marcuswu/Curta-Type-I-3x/Mods/Printed Lettering/selector shaft top/mmu selector shaft top.3mf

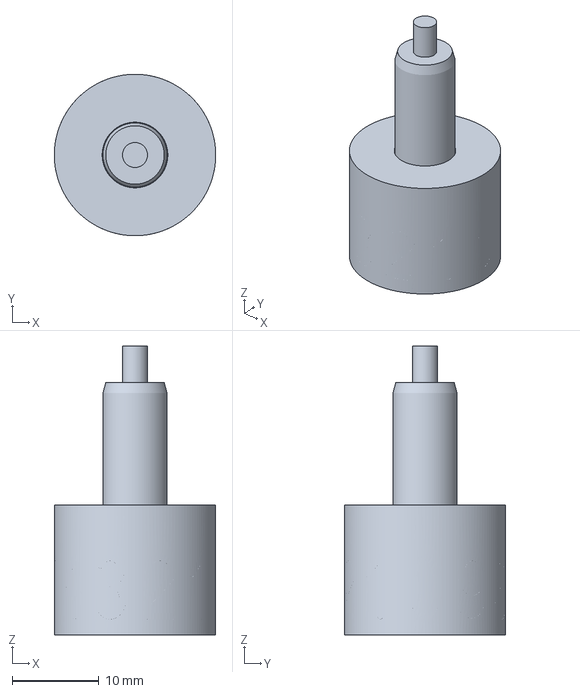
[picture p18: CAD file, 2025-07-06]
Mods/Printed Lettering/selector shaft top/mmu selector shaft top.3mf
18.6 x 18.6 x 33.3 mm
