marcuswu/Curta-Type-I-3x/Mods/Printed Lettering/upper housing/upper housing - digit 7.stl

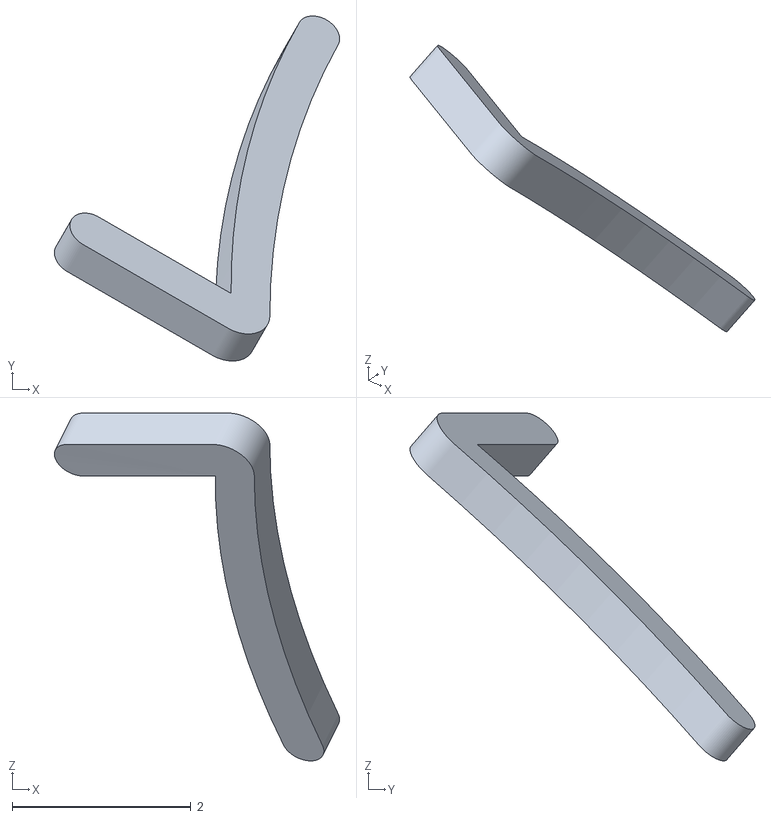
[picture p19: CAD file, 2025-07-06]
Mods/Printed Lettering/upper housing/upper housing - digit 7.stl
3.19 x 3.86 x 3.89
