marcuswu/Curta-Type-I-3x/Mods/Printed Lettering/upper outer sleeve/upper outer sleeve - A.stl

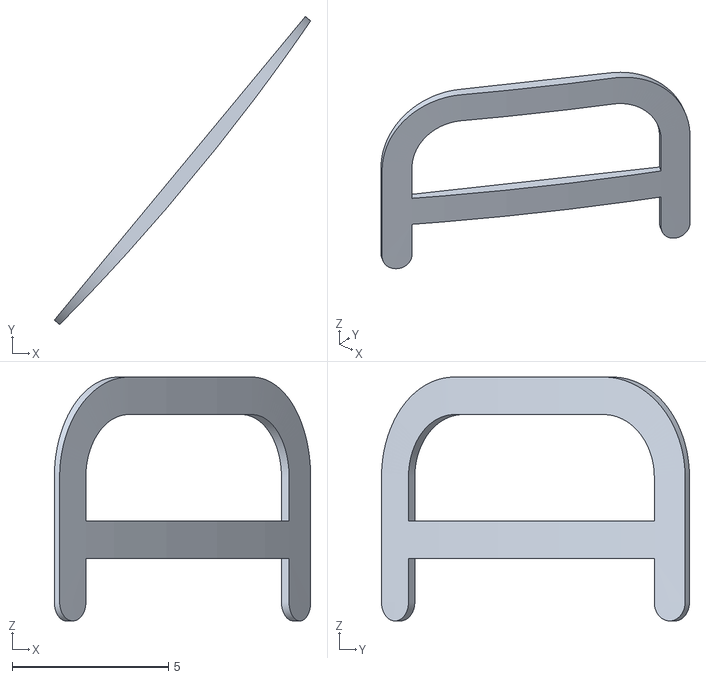
[picture p20: CAD file, 2025-07-06]
Mods/Printed Lettering/upper outer sleeve/upper outer sleeve - A.stl
8.20 x 9.85 x 7.80
