marcuswu/Curta-Type-I-3x/STLs/10 - Upper Frame/frame support x3.stl

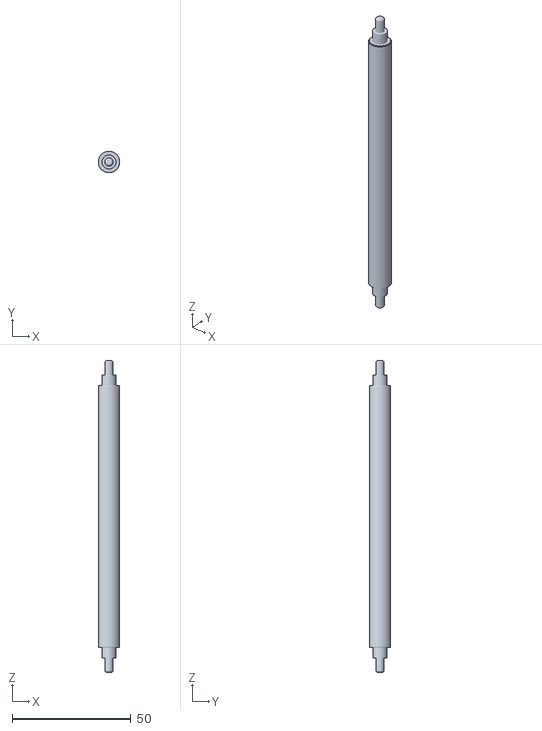
[picture p21: CAD file, 2022-03-31]
STLs/10 - Upper Frame/frame support x3.stl
9.00 x 9.00 x 131.2
