marcuswu/Curta-Type-I-3x/STLs/11 - Assemble Step Drum/step drum joining pin x3.stl

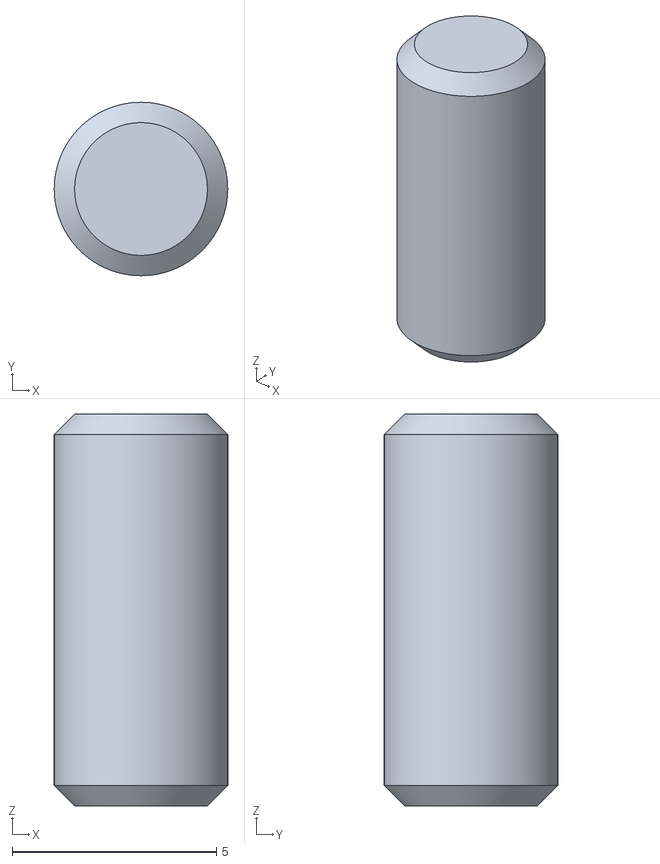
[picture p22: CAD file, 2022-03-31]
STLs/11 - Assemble Step Drum/step drum joining pin x3.stl
4.25 x 4.25 x 9.60
