marcuswu/Curta-Type-I-3x/STLs/12 - Step Drum & Bearing Plate/bearing plate.stl

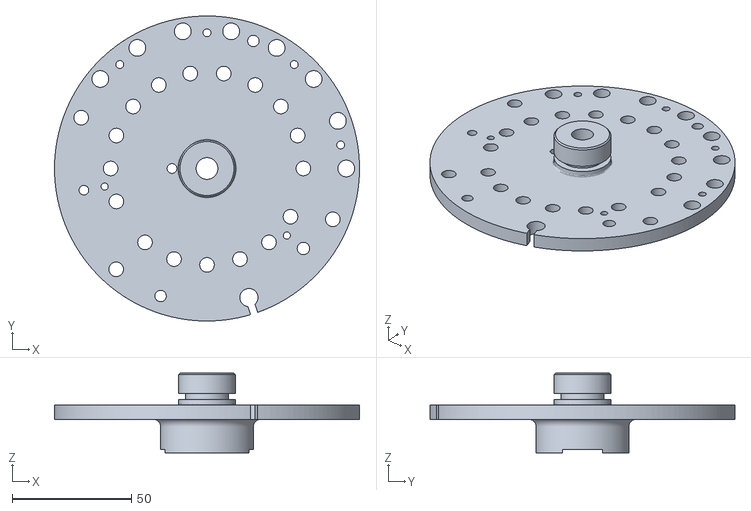
[picture p23: CAD file, 2022-03-31]
STLs/12 - Step Drum & Bearing Plate/bearing plate.stl
128.1 x 128.1 x 33.6
