marcuswu/Curta-Type-I-3x/STLs/15 - Zero Positioning Disc/zero positioning disc securing spring.stl

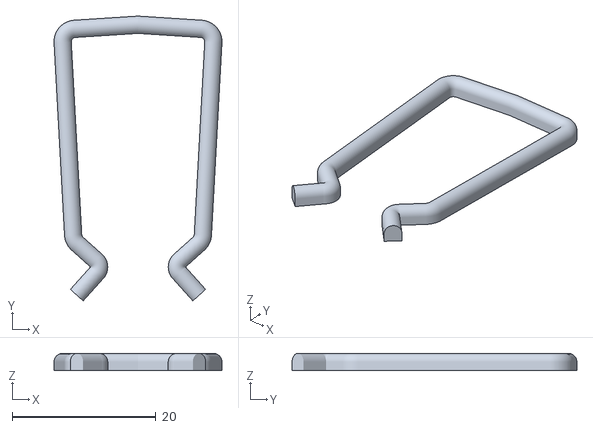
[picture p24: CAD file, 2022-03-31]
STLs/15 - Zero Positioning Disc/zero positioning disc securing spring.stl
23.3 x 39.6 x 2.40
