marcuswu/Curta-Type-I-3x/STLs/18 - Zero Positioning Disc Pin/zero positioning disc pin.stl

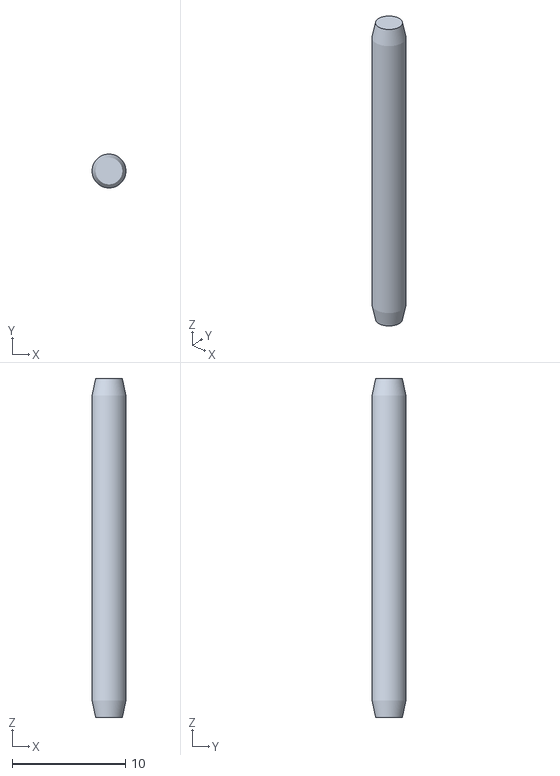
[picture p25: CAD file, 2022-03-31]
STLs/18 - Zero Positioning Disc Pin/zero positioning disc pin.stl
3.00 x 3.00 x 30.0
