marcuswu/Curta-Type-I-3x/STLs/21 - Transmission Shafts/transmission shaft 10208.stl

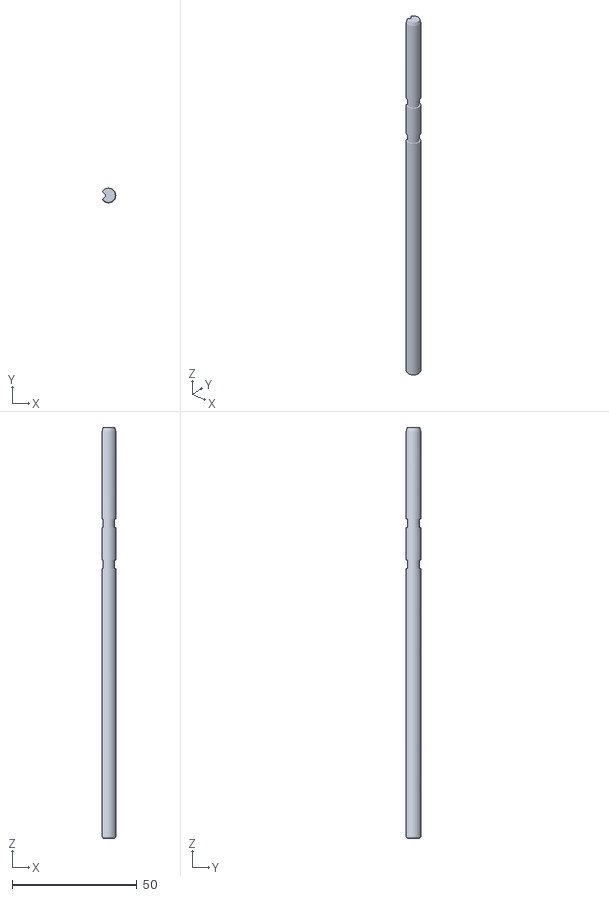
[picture p26: CAD file, 2022-03-31]
STLs/21 - Transmission Shafts/transmission shaft 10208.stl
5.45 x 5.89 x 165.0
