marcuswu/Curta-Type-I-3x/STLs/26 - Cover Ring/cover ring.stl

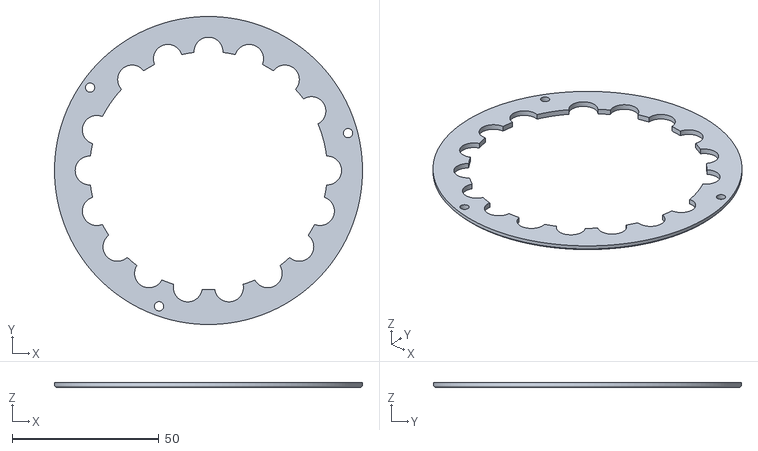
[picture p27: CAD file, 2022-03-31]
STLs/26 - Cover Ring/cover ring.stl
104.9 x 104.9 x 1.80
