marcuswu/Curta-Type-I-3x/STLs/27 - Assemble Reversing Lever/reversing lever knob.stl

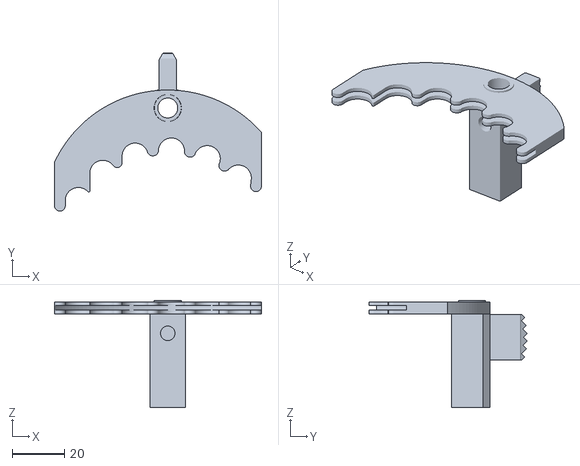
[picture p28: CAD file, 2022-03-31]
STLs/27 - Assemble Reversing Lever/reversing lever knob.stl
79.5 x 60.8 x 41.1
