marcuswu/Curta-Type-I-3x/STLs/29 - Assemble Carry Levers/tens slide bearing x15.stl

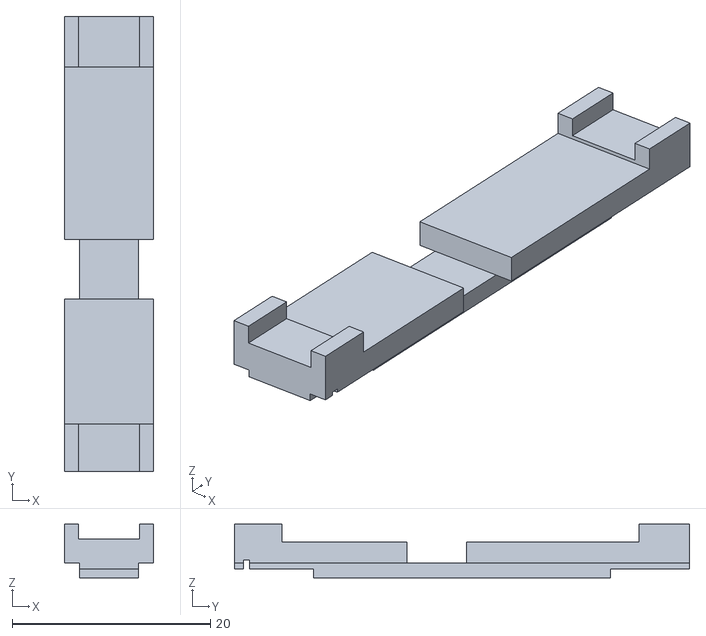
[picture p29: CAD file, 2022-03-31]
STLs/29 - Assemble Carry Levers/tens slide bearing x15.stl
9.00 x 45.9 x 5.40
