marcuswu/Curta-Type-I-3x/STLs/31 - Assemble Input Selectors/selector knob x8.stl

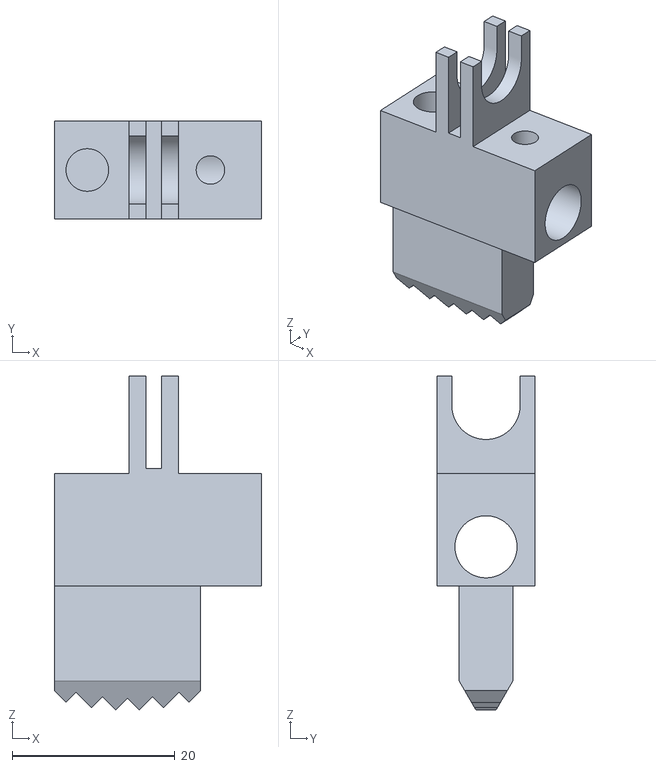
[picture p30: CAD file, 2022-03-31]
STLs/31 - Assemble Input Selectors/selector knob x8.stl
25.5 x 12.0 x 41.1
