marcuswu/Curta-Type-I-3x/STLs/32 - Input Selectors/selector shaft bearing x8.stl

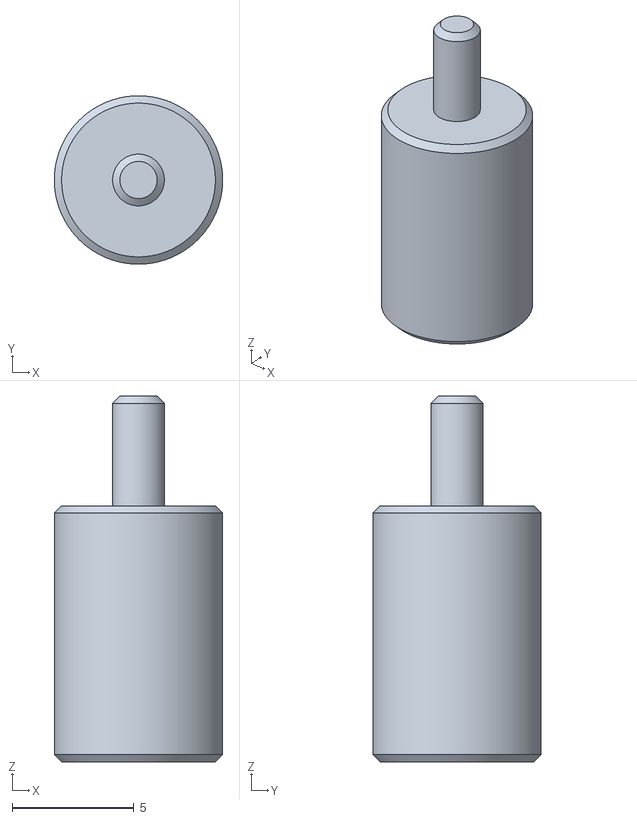
[picture p31: CAD file, 2022-03-31]
STLs/32 - Input Selectors/selector shaft bearing x8.stl
6.90 x 6.90 x 15.0
