marcuswu/Curta-Type-I-3x/STLs/33 - Upper Sleeve/upper outer sleeve.stl

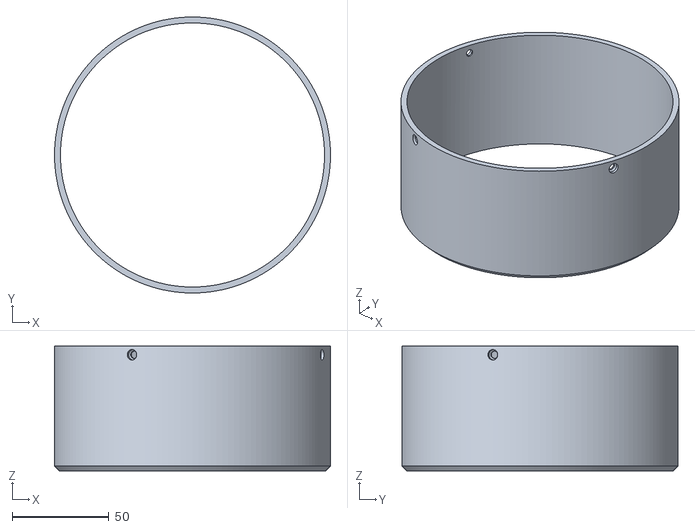
[picture p32: CAD file, 2022-03-31]
STLs/33 - Upper Sleeve/upper outer sleeve.stl
142.5 x 142.5 x 64.5
