marcuswu/Curta-Type-I-3x/STLs/34 - Lower Housing & Base Plate/lower housing.stl

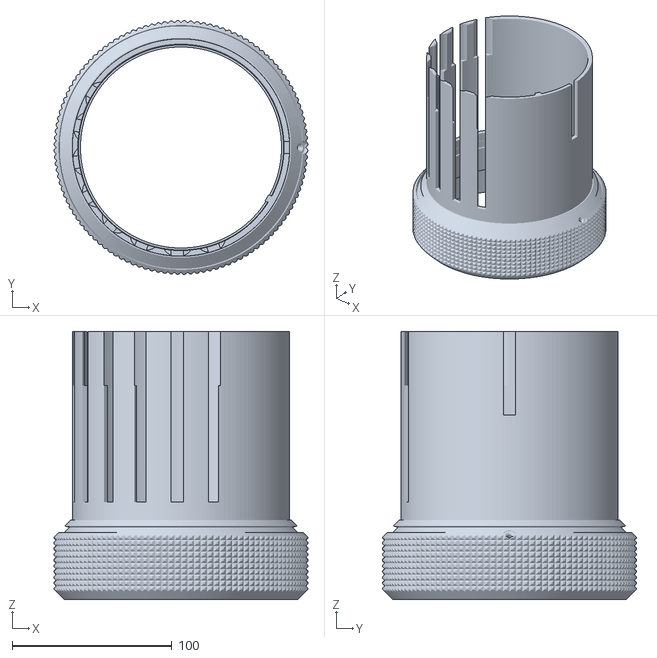
[picture p33: CAD file, 2022-03-31]
STLs/34 - Lower Housing & Base Plate/lower housing.stl
159.0 x 159.0 x 168.0
