marcuswu/Curta-Type-I-3x/STLs/37 - Clearing Cover/clearing cover.stl

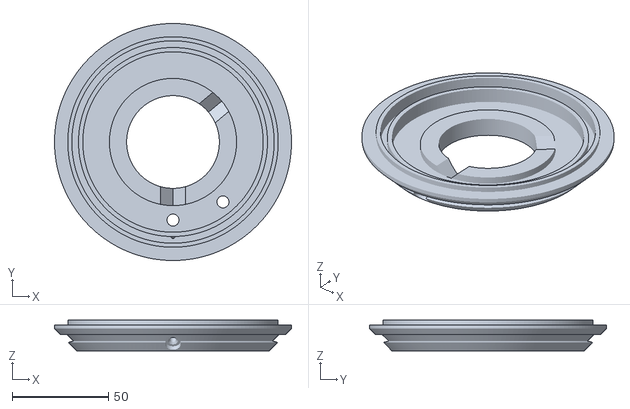
[picture p34: CAD file, 2022-03-31]
STLs/37 - Clearing Cover/clearing cover.stl
123.0 x 123.0 x 15.9
