marcuswu/Curta-Type-I-3x/STLs/38 - Carriage Body/carriage body.stl

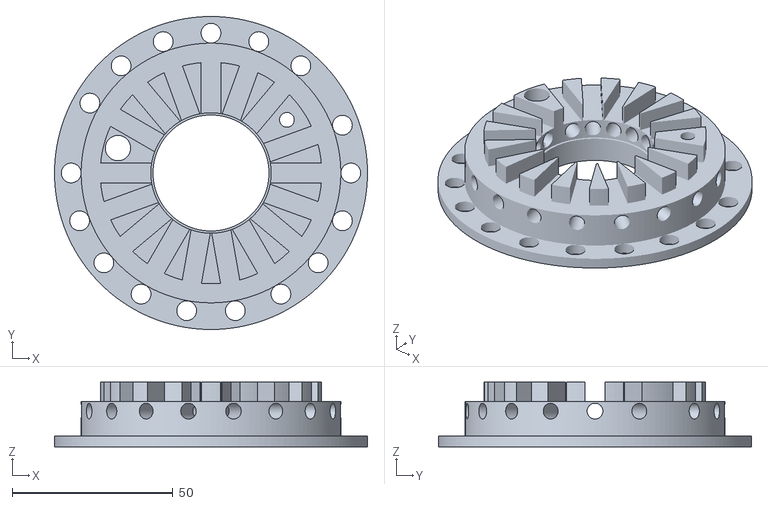
[picture p35: CAD file, 2022-03-31]
STLs/38 - Carriage Body/carriage body.stl
97.5 x 97.5 x 20.1
