marcuswu/Curta-Type-I-3x/STLs/39 - Clearing Stop Pin & Digit Axles/digits axle x17.stl

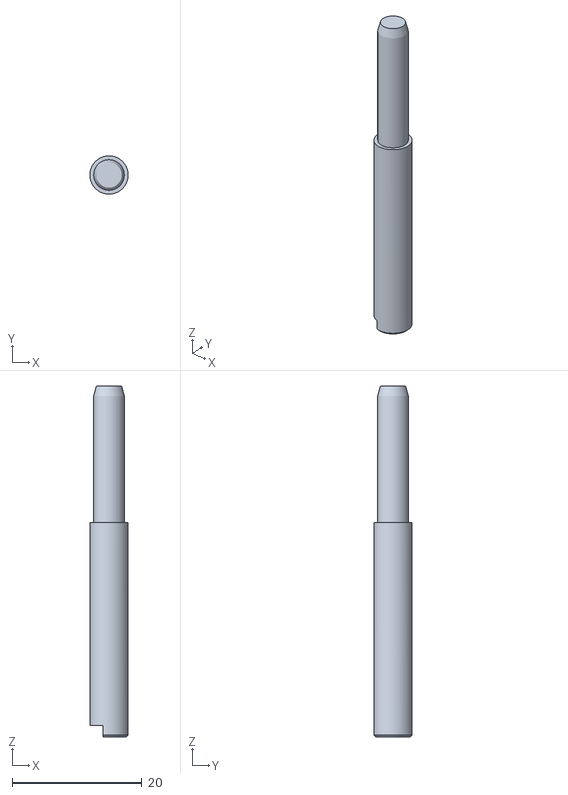
[picture p36: CAD file, 2022-03-31]
STLs/39 - Clearing Stop Pin & Digit Axles/digits axle x17.stl
5.89 x 5.89 x 54.0
