marcuswu/Curta-Type-I-3x/STLs/41 - Spider Spring/spider spring.stl

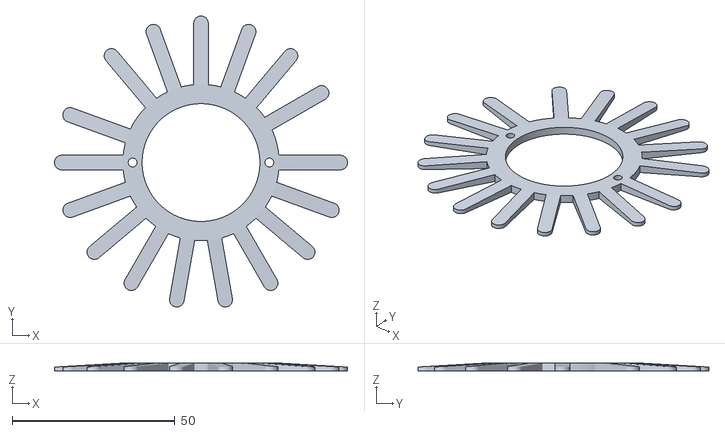
[picture p37: CAD file, 2022-03-31]
STLs/41 - Spider Spring/spider spring.stl
90.0 x 89.4 x 2.42
