marcuswu/Curta-Type-I-3x/STLs/42 - Digit Cover & Upper Housing/upper housing.stl

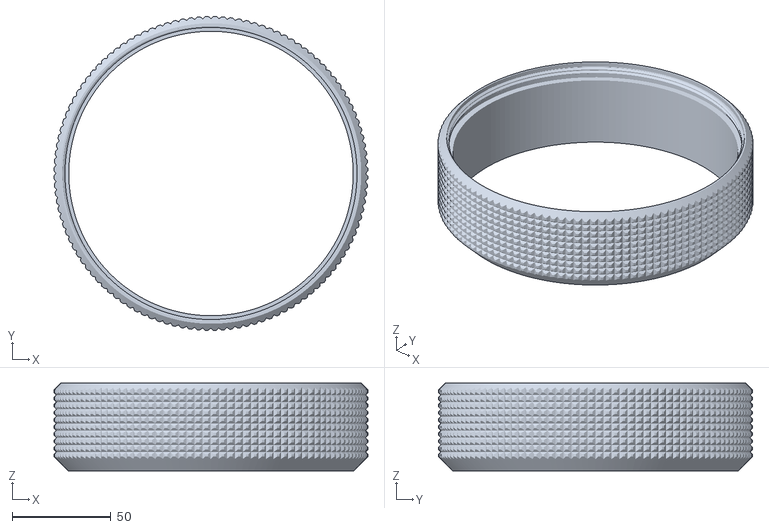
[picture p38: CAD file, 2022-03-31]
STLs/42 - Digit Cover & Upper Housing/upper housing.stl
159.0 x 159.0 x 44.4
