marcuswu/Curta-Type-I-3x/STLs/47 - Carriage Spring/spring sleeve c-clip.stl

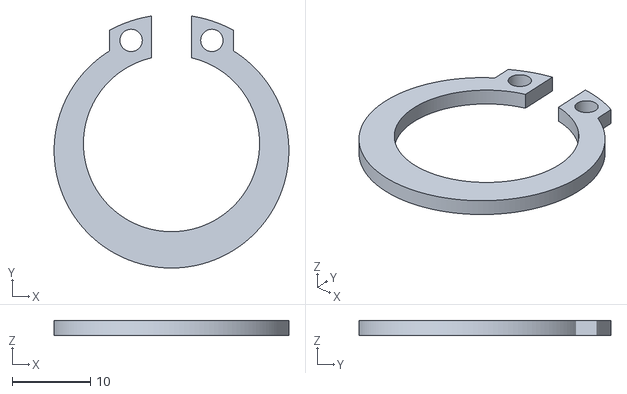
[picture p39: CAD file, 2022-03-31]
STLs/47 - Carriage Spring/spring sleeve c-clip.stl
30.0 x 32.2 x 1.95
