marcuswu/Curta-Type-I-3x/STLs/49 - Crank Handle/crank handle pin.stl

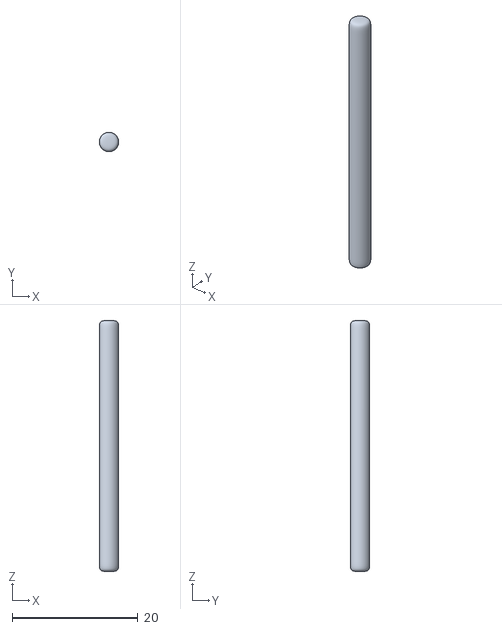
[picture p40: CAD file, 2022-03-31]
STLs/49 - Crank Handle/crank handle pin.stl
3.10 x 3.10 x 40.0
