marcuswu/Curta-Type-I-3x/STLs/50 - Decimal Markers/position marker x10.stl

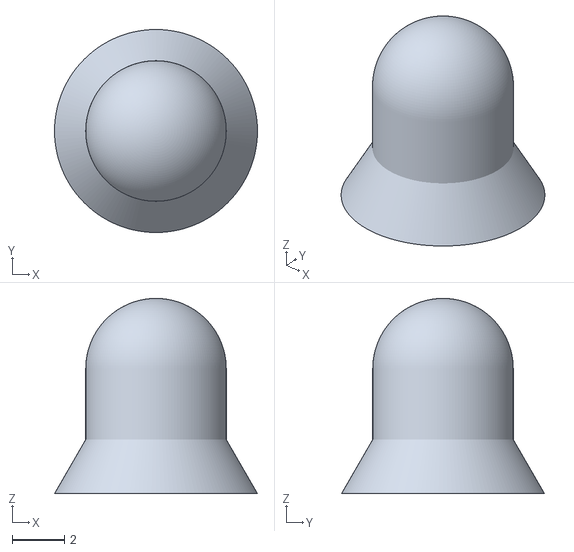
[picture p41: CAD file, 2022-03-31]
STLs/50 - Decimal Markers/position marker x10.stl
7.80 x 7.80 x 7.50
