marcuswu/Curta-Type-I-3x/STLs/8 - Assemble Tens Bell/tens bell.stl

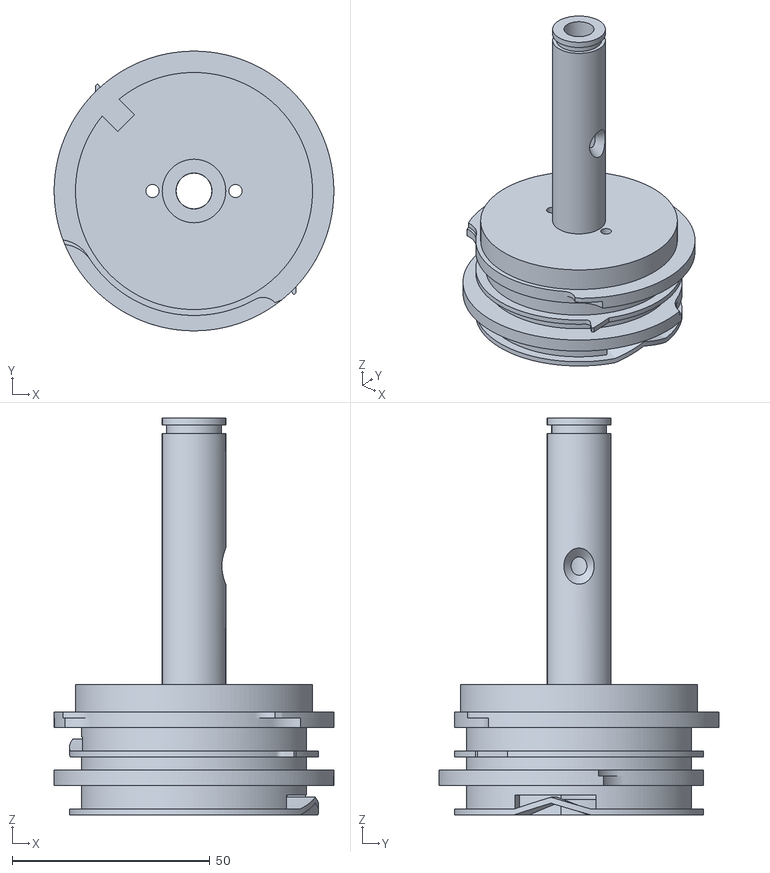
[picture p42: CAD file, 2022-03-31]
STLs/8 - Assemble Tens Bell/tens bell.stl
70.8 x 70.8 x 100.5
