marcuswu/Curta-Type-I-3x/STLs/9 - Tens Bell & Main Body/tens bell c-clip.stl

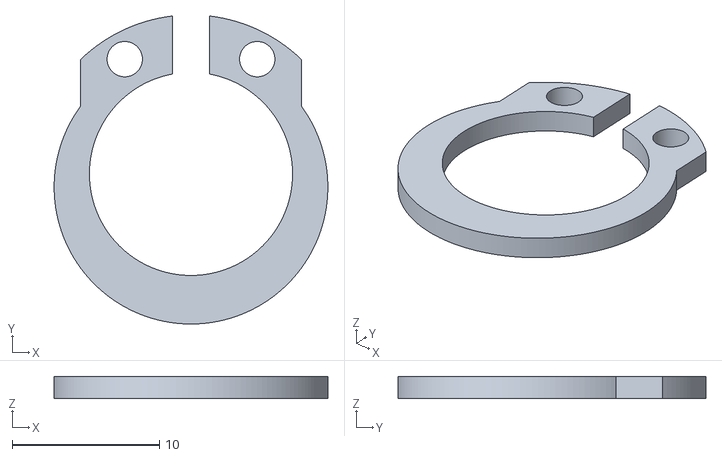
[picture p43: CAD file, 2022-03-31]
STLs/9 - Tens Bell & Main Body/tens bell c-clip.stl
18.6 x 20.9 x 1.50
