marcuswu/Curta-Type-I-3x/Manual/Painting/upper outer sleeve.dxf

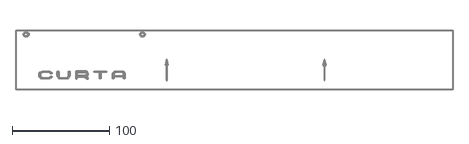
[picture p44: CAD file, 2025-07-06]
Manual/Painting/upper outer sleeve.dxf
448.0 x 61.5
