marcuswu/Curta-Type-I-3x/Mods/Metal Main Shaft/step_drum_top.stl

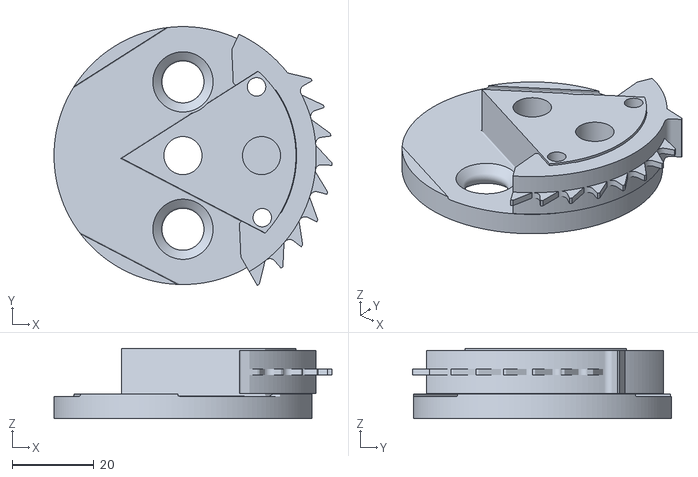
[picture p45: CAD file, 2025-07-06]
Mods/Metal Main Shaft/step_drum_top.stl
67.9 x 63.2 x 17.1
