marcuswu/Curta-Type-I-3x/Mods/Printed Lettering/lower housing/Lower Housing - input 2.stl

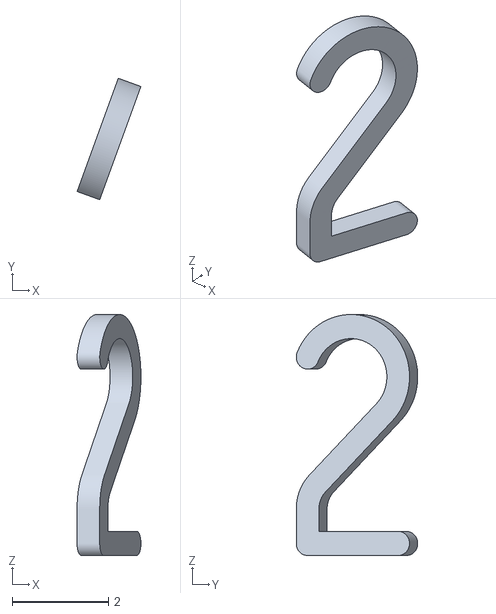
[picture p47: CAD file, 2025-07-06]
Mods/Printed Lettering/lower housing/Lower Housing - input 2.stl
1.32 x 2.52 x 5.00
