marcuswu/Curta-Type-I-3x/Mods/Printed Lettering/selector shaft top/selector shaft top - digit 5.stl

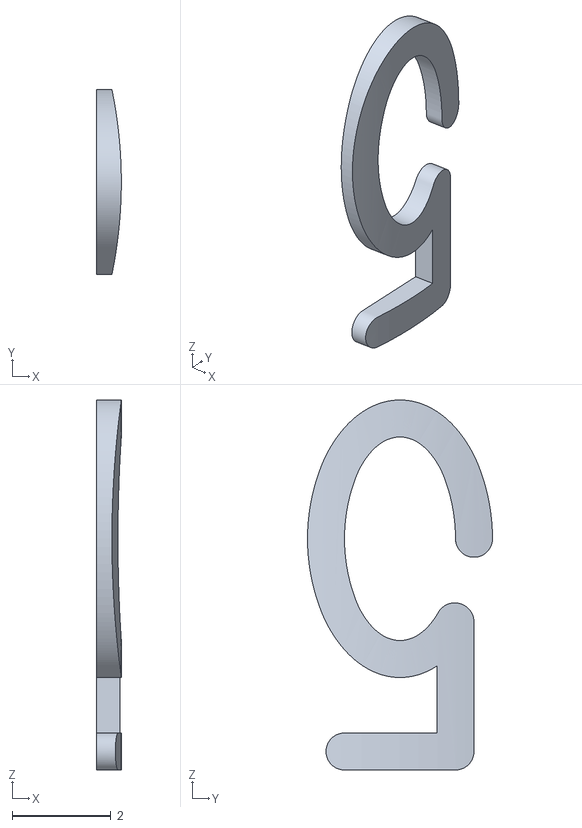
[picture p48: CAD file, 2025-07-06]
Mods/Printed Lettering/selector shaft top/selector shaft top - digit 5.stl
0.5 x 3.75 x 7.50
