marcuswu/Curta-Type-I-3x/Mods/Printed Lettering/upper housing/upper housing - digit 8.stl

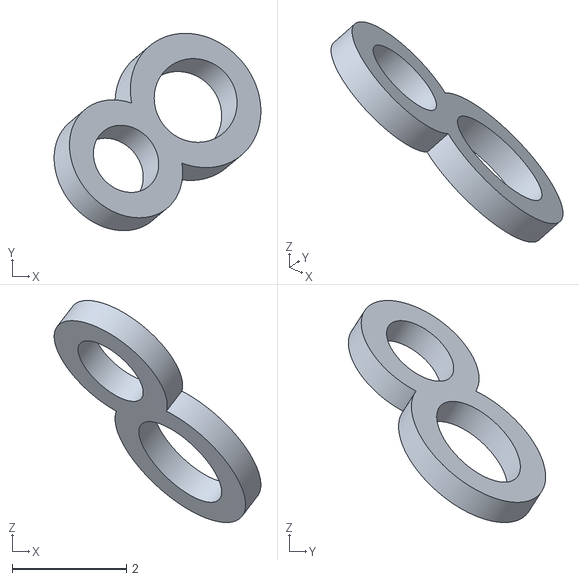
[picture p49: CAD file, 2025-07-06]
Mods/Printed Lettering/upper housing/upper housing - digit 8.stl
3.62 x 3.46 x 3.89
