marcuswu/Curta-Type-I-3x/STLs/12 - Step Drum & Bearing Plate/reverse nose plate.stl

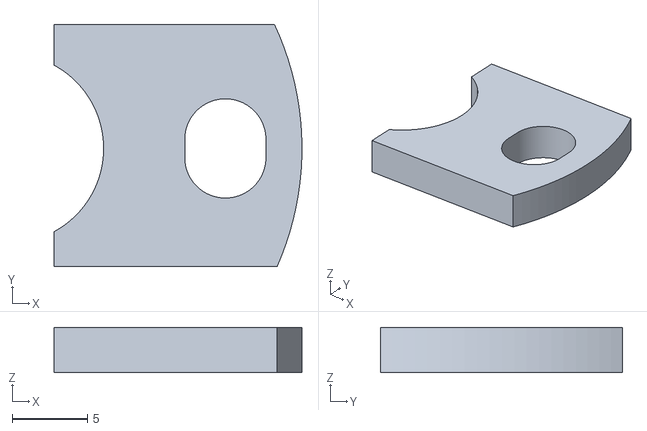
[picture p50: CAD file, 2022-03-31]
STLs/12 - Step Drum & Bearing Plate/reverse nose plate.stl
16.5 x 16.1 x 3.00
