marcuswu/Curta-Type-I-3x/STLs/15 - Zero Positioning Disc/zero positioning disc.stl

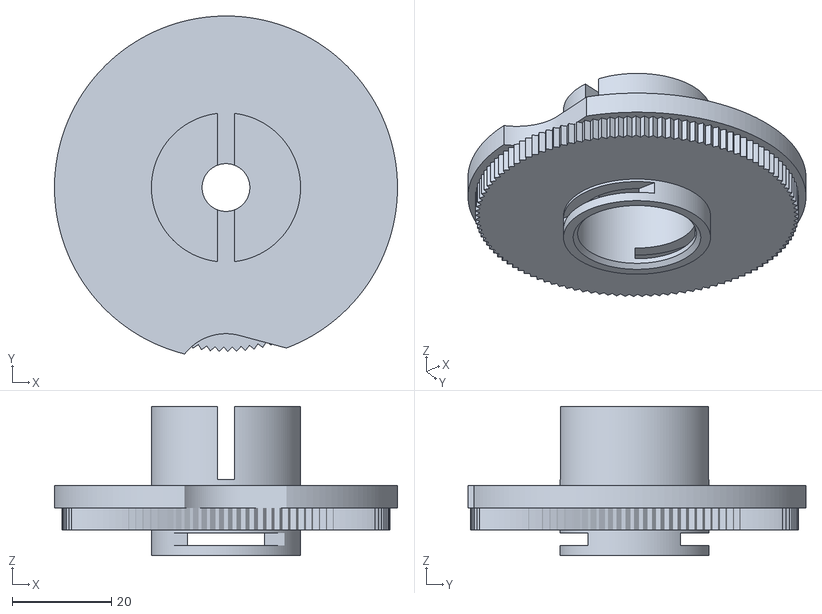
[picture p51: CAD file, 2022-03-31]
STLs/15 - Zero Positioning Disc/zero positioning disc.stl
69.0 x 68.0 x 30.0
