marcuswu/Curta-Type-I-3x/STLs/16 - Anti-Reversal Pawl/reverse rotation prevention pawl.stl

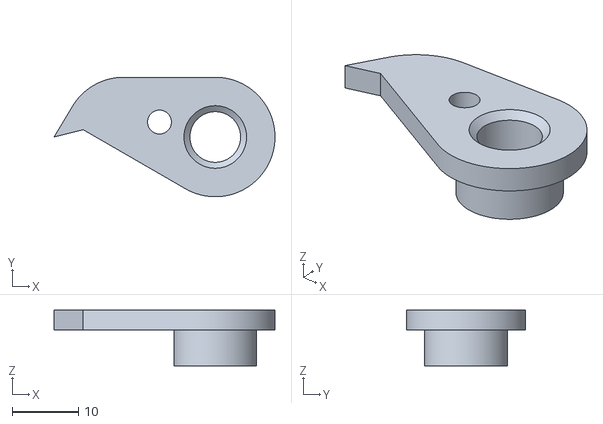
[picture p52: CAD file, 2022-03-31]
STLs/16 - Anti-Reversal Pawl/reverse rotation prevention pawl.stl
33.3 x 18.0 x 8.40
