marcuswu/Curta-Type-I-3x/STLs/21 - Transmission Shafts/transmission gear tip x17.stl

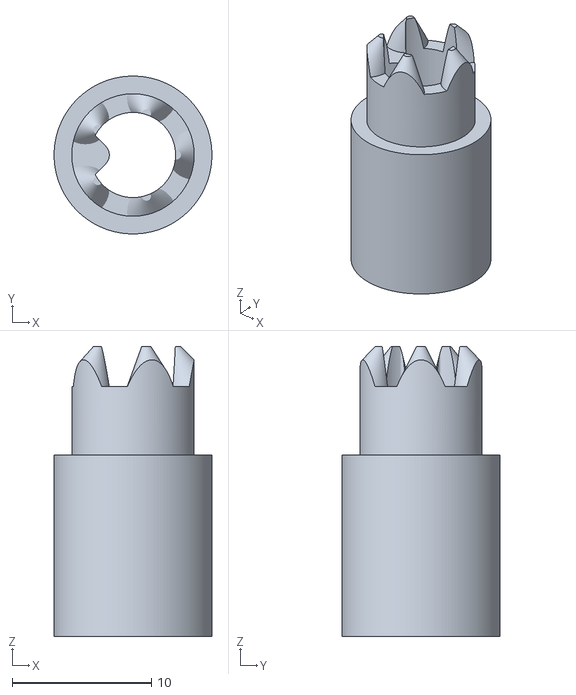
[picture p53: CAD file, 2022-03-31]
STLs/21 - Transmission Shafts/transmission gear tip x17.stl
11.4 x 11.4 x 20.8
