marcuswu/Curta-Type-I-3x/STLs/29 - Assemble Carry Levers/tens slider for turns counter x5.stl

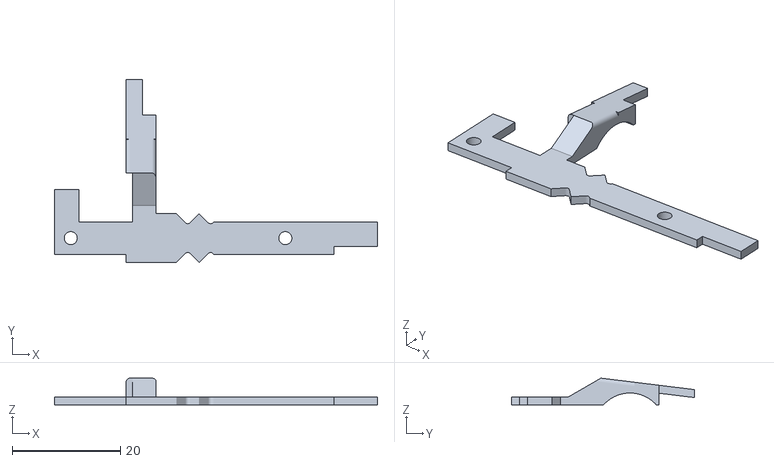
[picture p55: CAD file, 2022-03-31]
STLs/29 - Assemble Carry Levers/tens slider for turns counter x5.stl
59.6 x 33.8 x 4.93
