marcuswu/Curta-Type-I-3x/STLs/32 - Input Selectors/setting axle holding plate x2.stl

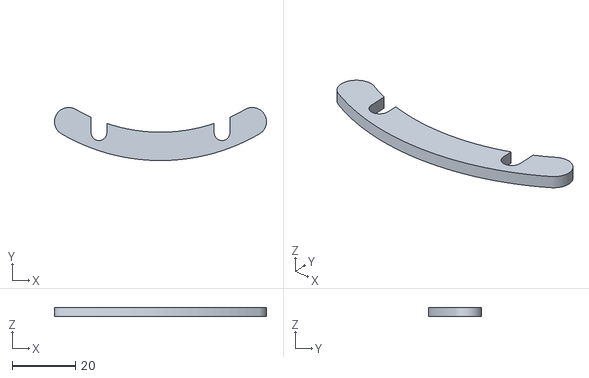
[picture p56: CAD file, 2022-03-31]
STLs/32 - Input Selectors/setting axle holding plate x2.stl
67.2 x 16.8 x 3.00
