marcuswu/Curta-Type-I-3x/STLs/34 - Lower Housing & Base Plate/base plate.stl

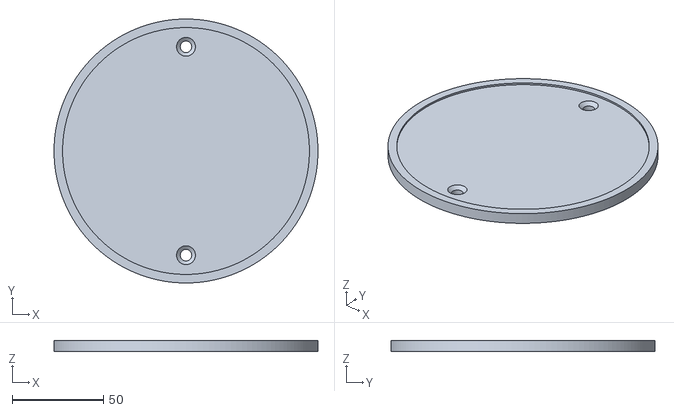
[picture p57: CAD file, 2022-03-31]
STLs/34 - Lower Housing & Base Plate/base plate.stl
144.4 x 144.4 x 6.00
