marcuswu/Curta-Type-I-3x/STLs/36 - Results Dials/results dial 10043 x4.stl

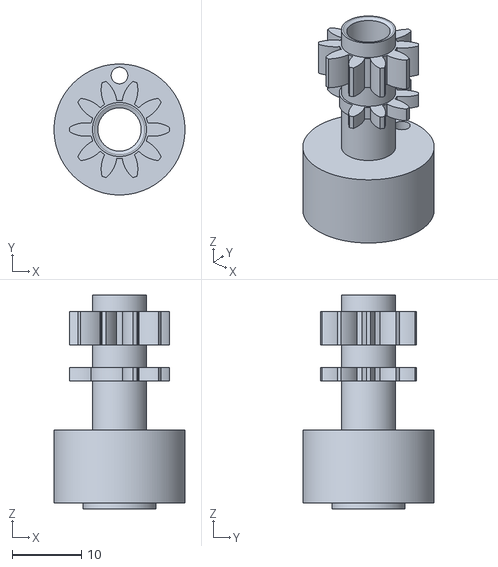
[picture p58: CAD file, 2022-03-31]
STLs/36 - Results Dials/results dial 10043 x4.stl
18.9 x 18.9 x 30.9
