marcuswu/Curta-Type-I-3x/STLs/37 - Clearing Cover/clearing cap tooth segment spacer.stl

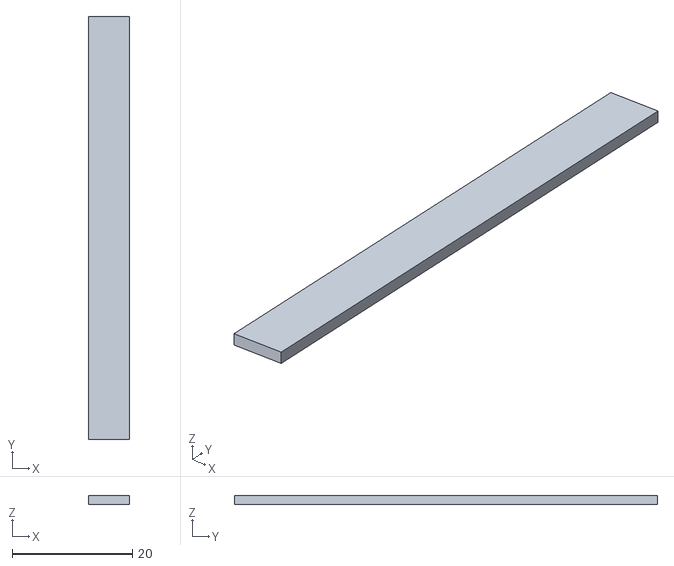
[picture p59: CAD file, 2022-03-31]
STLs/37 - Clearing Cover/clearing cap tooth segment spacer.stl
6.90 x 70.5 x 1.50
