marcuswu/Curta-Type-I-3x/STLs/38 - Carriage Body/clearing stop pin.stl

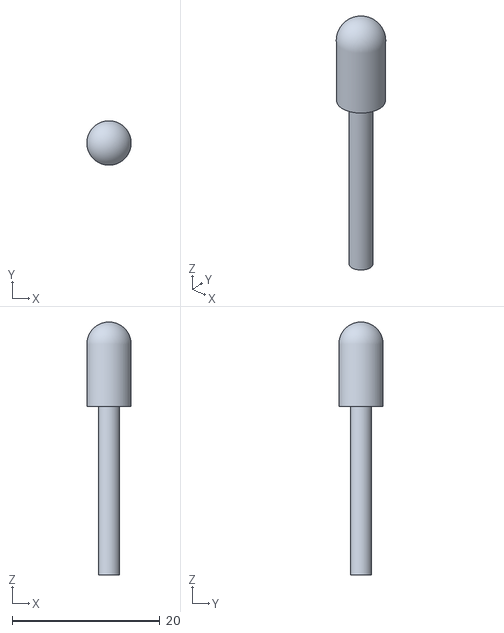
[picture p60: CAD file, 2022-03-31]
STLs/38 - Carriage Body/clearing stop pin.stl
6.00 x 6.00 x 34.2
