marcuswu/Curta-Type-I-3x/STLs/39 - Clearing Stop Pin & Digit Axles/carriage body stop pin.stl

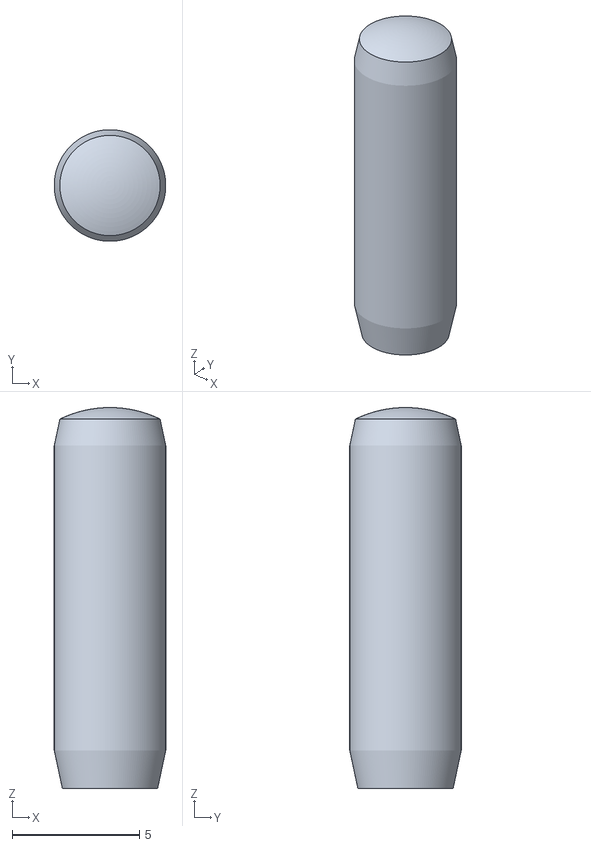
[picture p61: CAD file, 2022-03-31]
STLs/39 - Clearing Stop Pin & Digit Axles/carriage body stop pin.stl
4.39 x 4.39 x 15.0
