marcuswu/Curta-Type-I-3x/STLs/42 - Digit Cover & Upper Housing/digits cover.stl

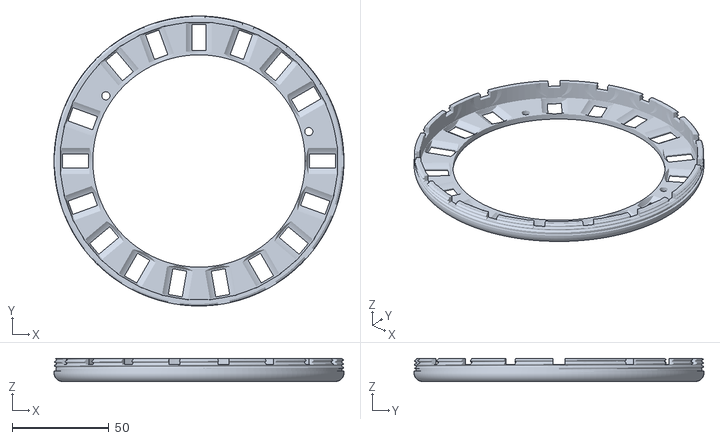
[picture p62: CAD file, 2022-03-31]
STLs/42 - Digit Cover & Upper Housing/digits cover.stl
150.0 x 150.0 x 12.0
