marcuswu/Curta-Type-I-3x/STLs/47 - Carriage Spring/thrust ring.stl

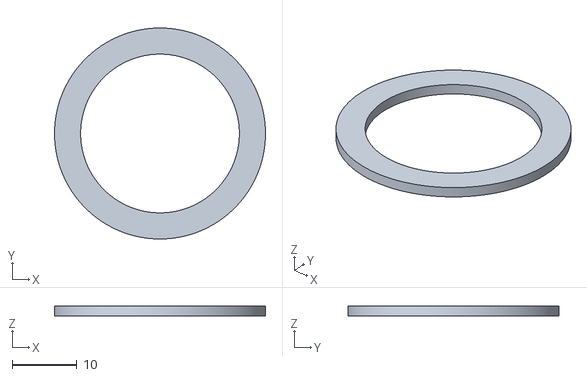
[picture p63: CAD file, 2022-03-31]
STLs/47 - Carriage Spring/thrust ring.stl
32.7 x 32.7 x 1.50
