marcuswu/Curta-Type-I-3x/STLs/8 - Assemble Tens Bell/tens bell spring.stl

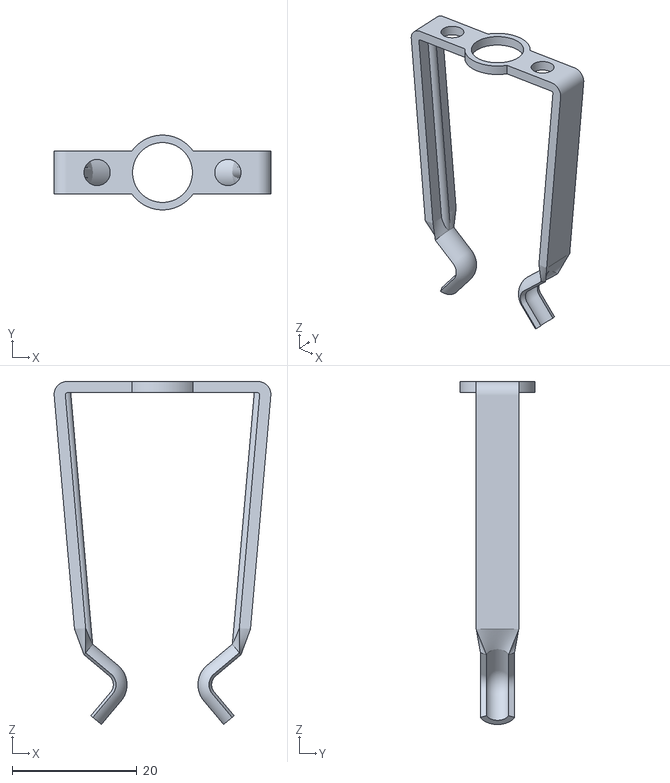
[picture p64: CAD file, 2022-03-31]
STLs/8 - Assemble Tens Bell/tens bell spring.stl
34.8 x 12.0 x 55.1
