marcuswu/Curta-Type-I-3x/STLs/9 - Tens Bell & Main Body/retaining ring for tens bell.stl

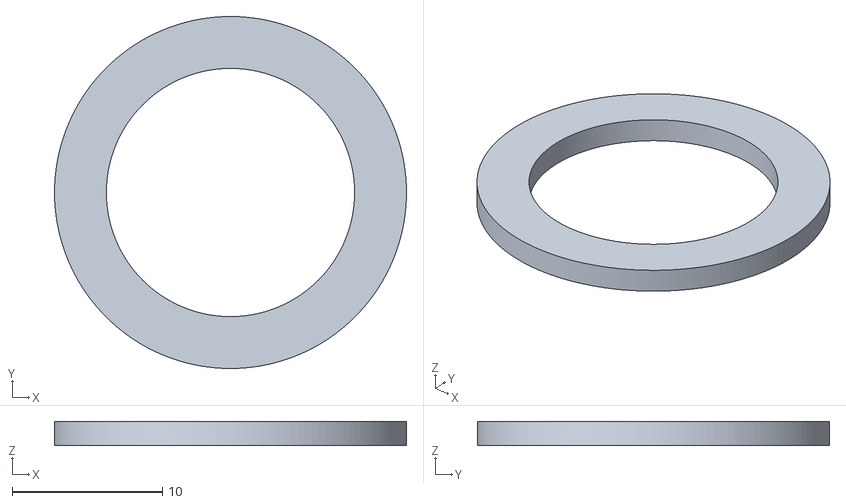
[picture p65: CAD file, 2022-03-31]
STLs/9 - Tens Bell & Main Body/retaining ring for tens bell.stl
23.4 x 23.4 x 1.60
