marcuswu/Curta-Type-I-3x/Manual/Painting/results dial.dxf

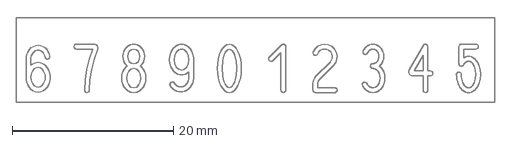
[picture p66: CAD file, 2025-07-06]
Manual/Painting/results dial.dxf
59.4 x 10.5 mm
