marcuswu/Curta-Type-I-3x/Mods/Metal Main Shaft/step_drum_bottom.stl

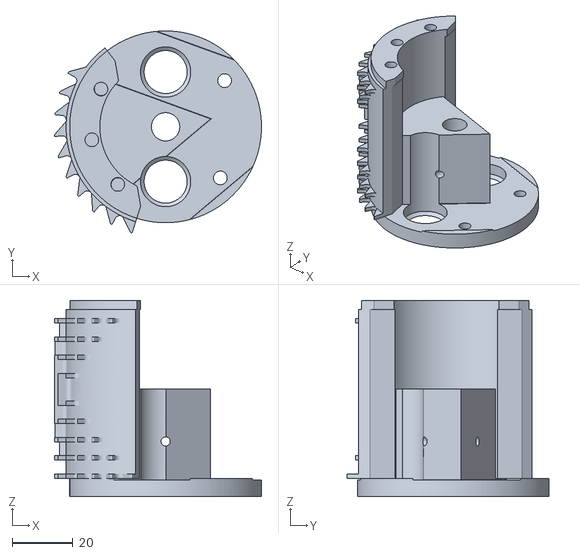
[picture p67: CAD file, 2025-07-06]
Mods/Metal Main Shaft/step_drum_bottom.stl
68.0 x 66.4 x 64.5
