marcuswu/Curta-Type-I-3x/Mods/Printed Lettering/lower housing/Lower Housing - input 5.stl

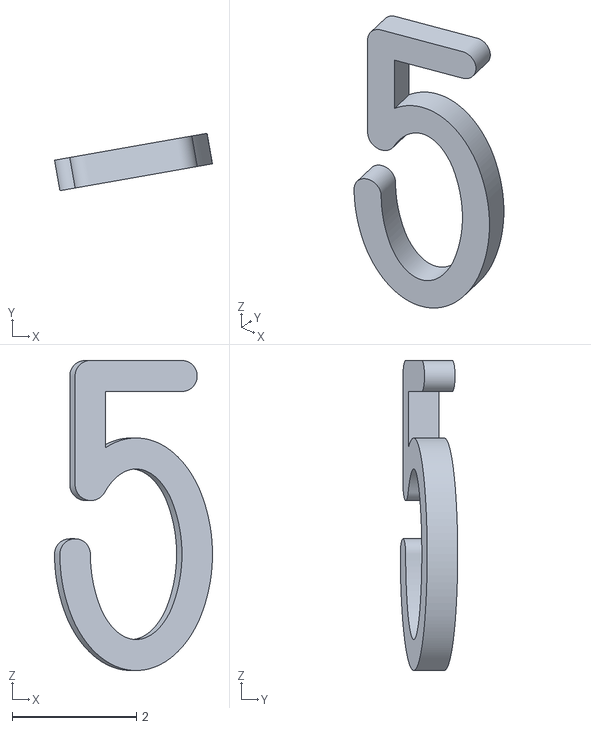
[picture p69: CAD file, 2025-07-06]
Mods/Printed Lettering/lower housing/Lower Housing - input 5.stl
2.55 x 0.927 x 5.00
