marcuswu/Curta-Type-I-3x/Mods/Printed Lettering/selector shaft top/selector shaft top.stl

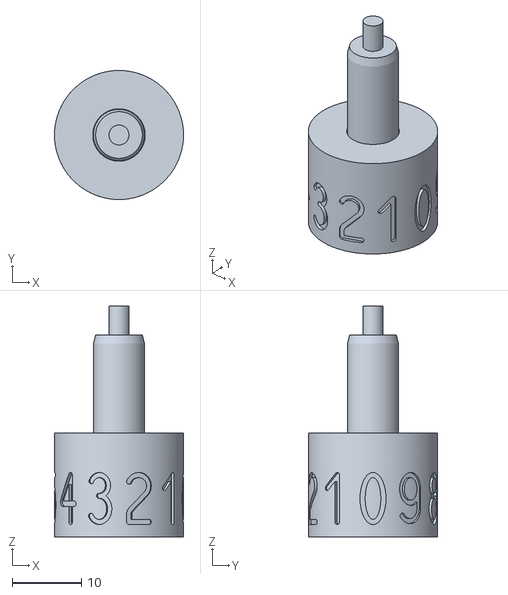
[picture p70: CAD file, 2025-07-06]
Mods/Printed Lettering/selector shaft top/selector shaft top.stl
18.6 x 18.6 x 33.3
