marcuswu/Curta-Type-I-3x/Mods/Printed Lettering/upper housing/upper housing - digit 6.stl

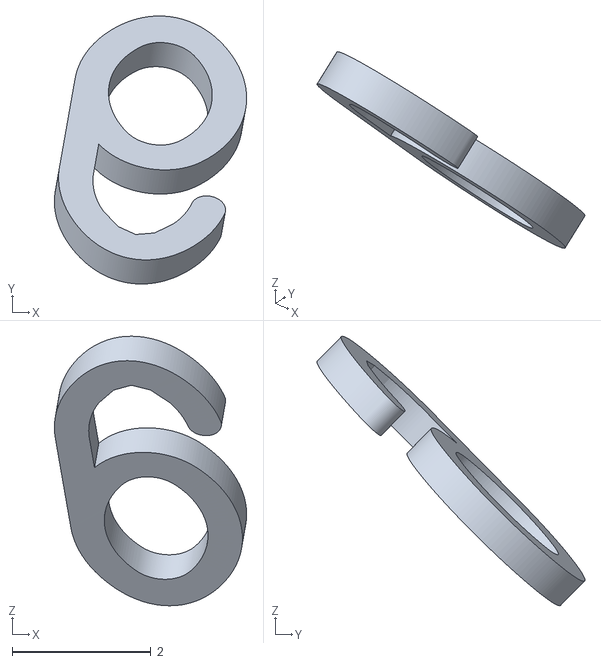
[picture p71: CAD file, 2025-07-06]
Mods/Printed Lettering/upper housing/upper housing - digit 6.stl
2.77 x 3.87 x 3.89
