marcuswu/Curta-Type-I-3x/STLs/13 - Assemble Zero Positioning Lever/zero positioning disc roller.stl

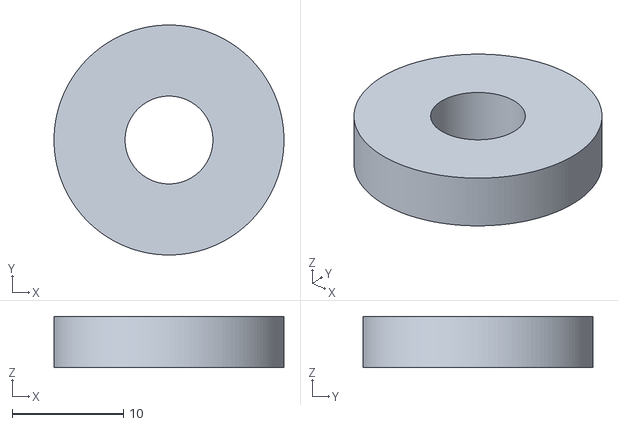
[picture p72: CAD file, 2022-03-31]
STLs/13 - Assemble Zero Positioning Lever/zero positioning disc roller.stl
20.7 x 20.7 x 4.60
