marcuswu/Curta-Type-I-3x/STLs/27 - Assemble Reversing Lever/upper reversing lever spacer.stl

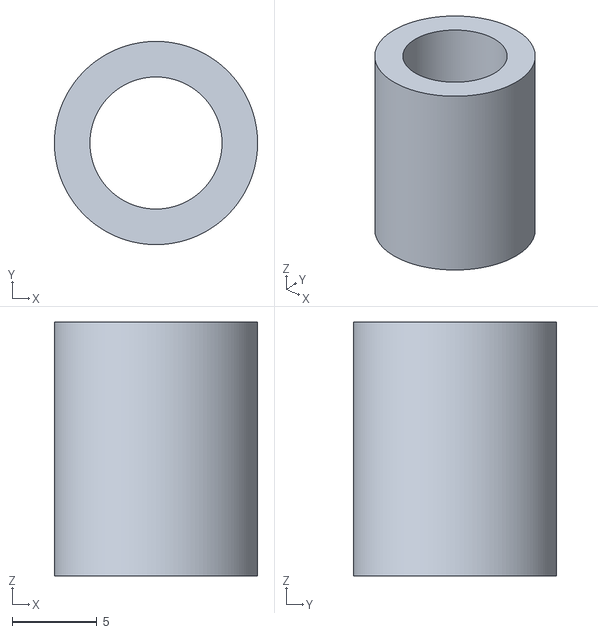
[picture p73: CAD file, 2022-03-31]
STLs/27 - Assemble Reversing Lever/upper reversing lever spacer.stl
12.0 x 12.0 x 15.0
