marcuswu/Curta-Type-I-3x/STLs/29 - Assemble Carry Levers/tens slider for results x10.stl

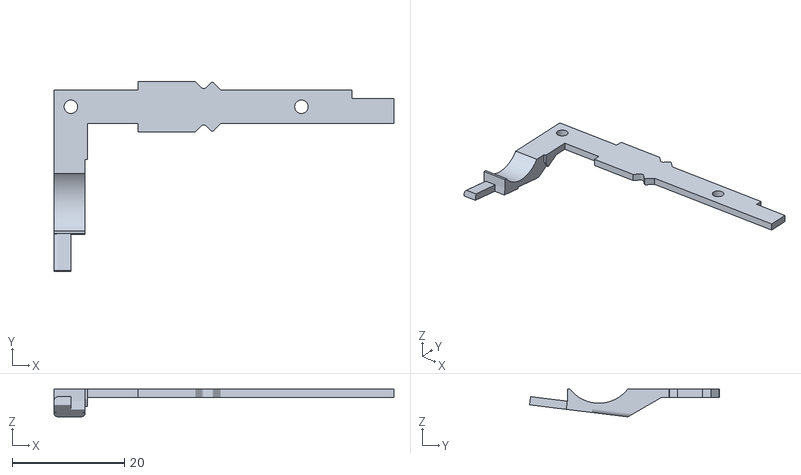
[picture p74: CAD file, 2022-03-31]
STLs/29 - Assemble Carry Levers/tens slider for results x10.stl
60.6 x 33.9 x 4.96
