marcuswu/Curta-Type-I-3x/STLs/31 - Assemble Input Selectors/selector shaft top x8.stl

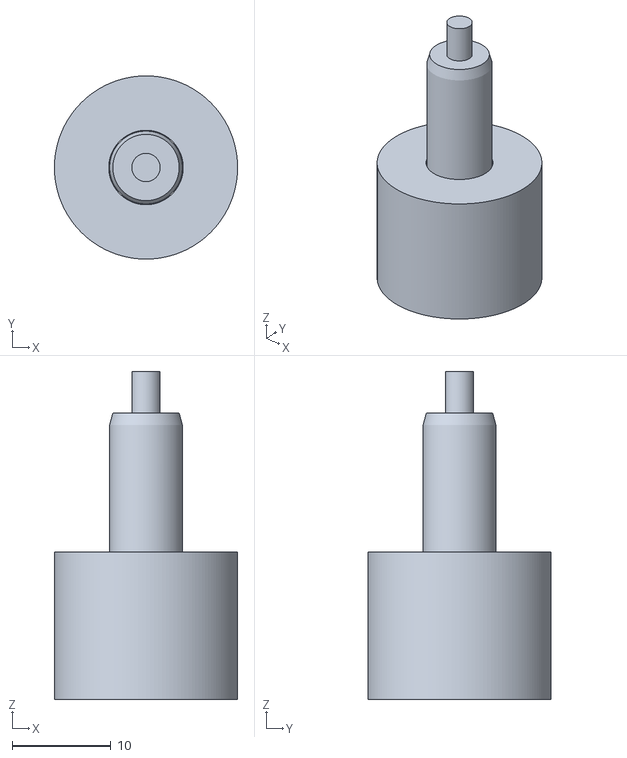
[picture p75: CAD file, 2022-03-31]
STLs/31 - Assemble Input Selectors/selector shaft top x8.stl
18.6 x 18.6 x 33.3
