marcuswu/Curta-Type-I-3x/STLs/36 - Results Dials/number roll carry pin half x8.stl

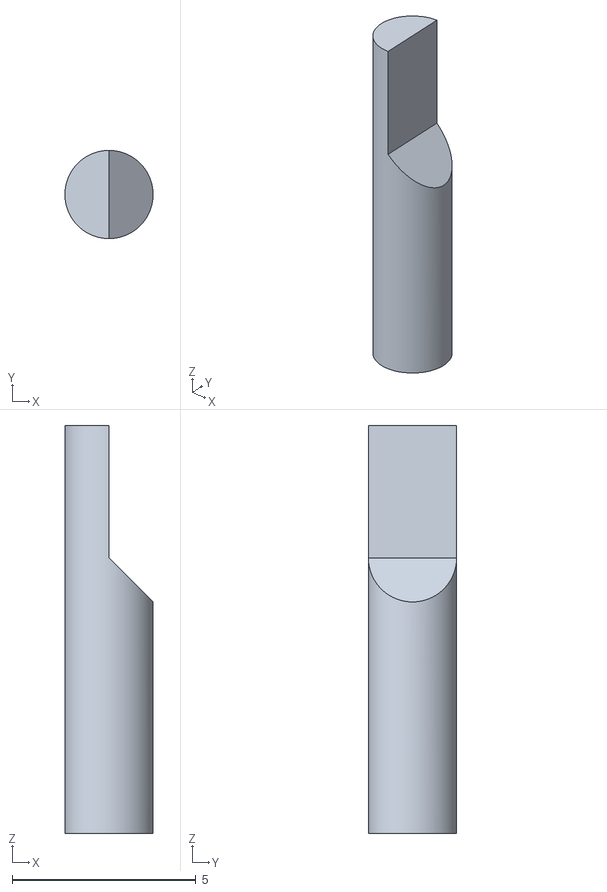
[picture p76: CAD file, 2022-03-31]
STLs/36 - Results Dials/number roll carry pin half x8.stl
2.40 x 2.40 x 11.1
