marcuswu/Curta-Type-I-3x/STLs/37 - Clearing Cover/clearing cap teeth x2.stl

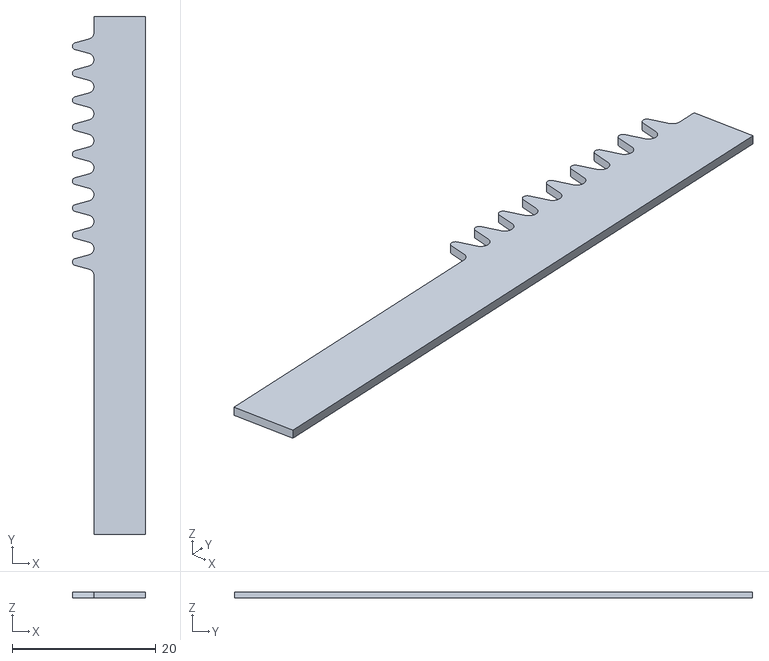
[picture p77: CAD file, 2022-03-31]
STLs/37 - Clearing Cover/clearing cap teeth x2.stl
10.2 x 72.0 x 0.9
