marcuswu/Curta-Type-I-3x/STLs/38 - Carriage Body/clearing stop pin sleeve.stl

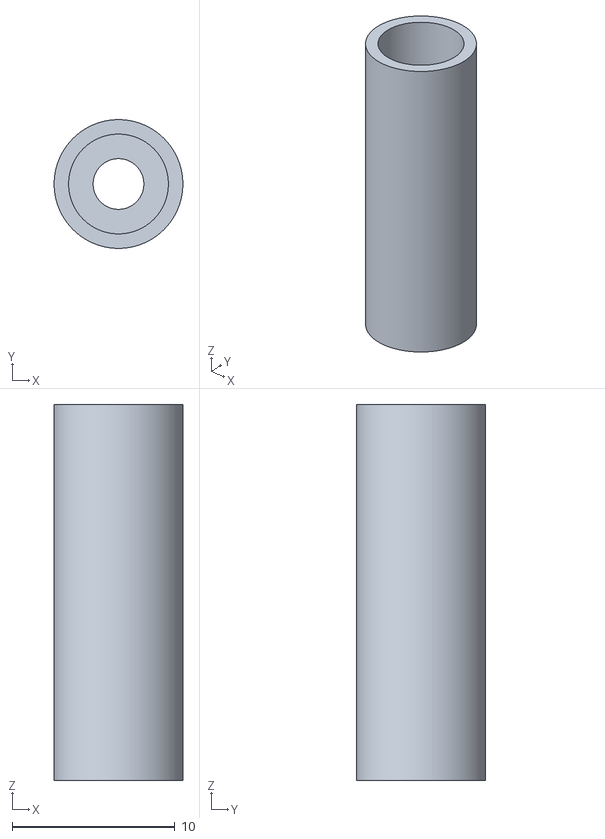
[picture p78: CAD file, 2022-03-31]
STLs/38 - Carriage Body/clearing stop pin sleeve.stl
7.91 x 7.91 x 23.1
