marcuswu/Curta-Type-I-3x/STLs/43 - Clearing Cover & Collar/crank collar.stl

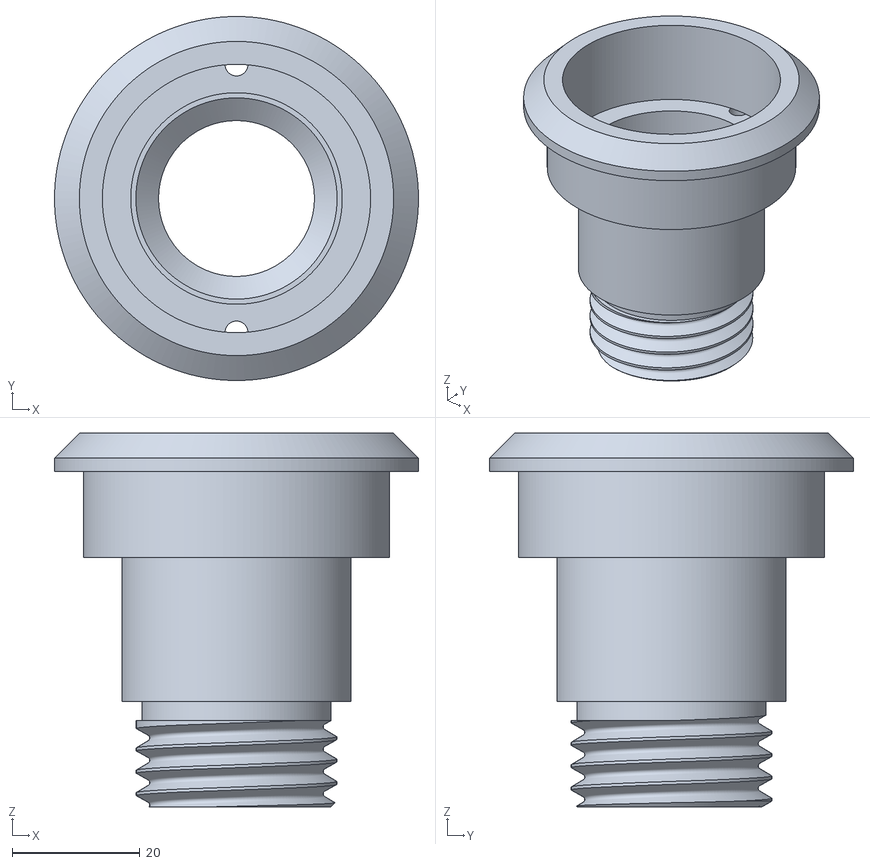
[picture p79: CAD file, 2022-03-31]
STLs/43 - Clearing Cover & Collar/crank collar.stl
57.0 x 57.0 x 58.5
