marcuswu/Curta-Type-I-3x/STLs/47 - Carriage Spring/carriage spring sleeve.stl

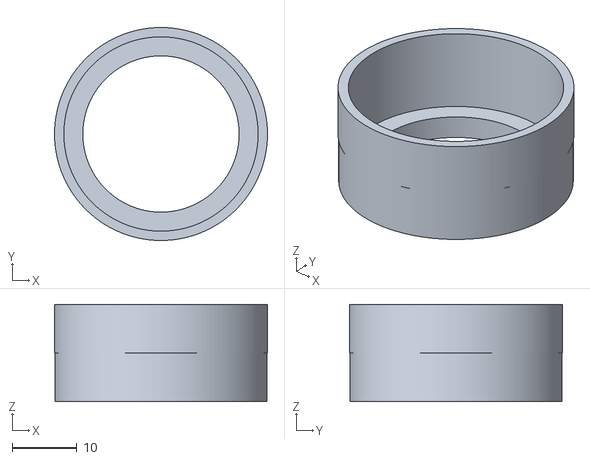
[picture p80: CAD file, 2022-03-31]
STLs/47 - Carriage Spring/carriage spring sleeve.stl
32.9 x 32.9 x 15.0
