marcuswu/Curta-Type-I-3x/STLs/48 - Assemble Crank Handle/crank handle.stl

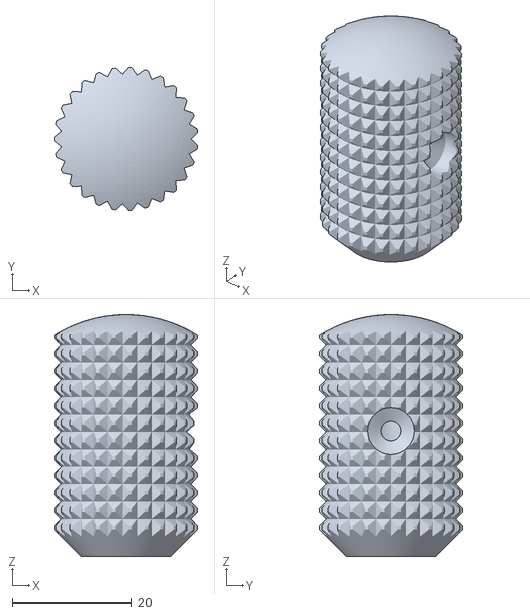
[picture p81: CAD file, 2022-03-31]
STLs/48 - Assemble Crank Handle/crank handle.stl
23.9 x 24.0 x 40.5
