marcuswu/Curta-Type-I-3x/Manual/Painting/Bottom disc.dxf

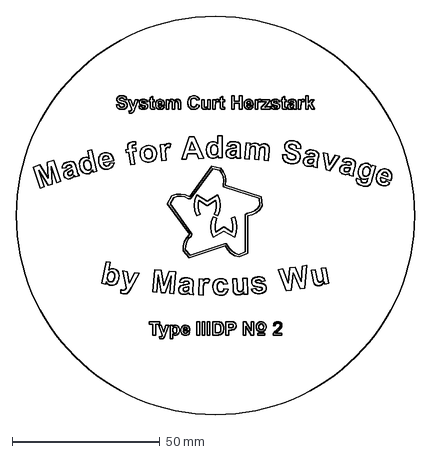
[picture p82: CAD file, 2025-07-06]
Manual/Painting/Bottom disc.dxf
135.0 x 135.0 mm
