marcuswu/Curta-Type-I-3x/Mods/Printed Lettering/dials/results dial - digit 3.stl

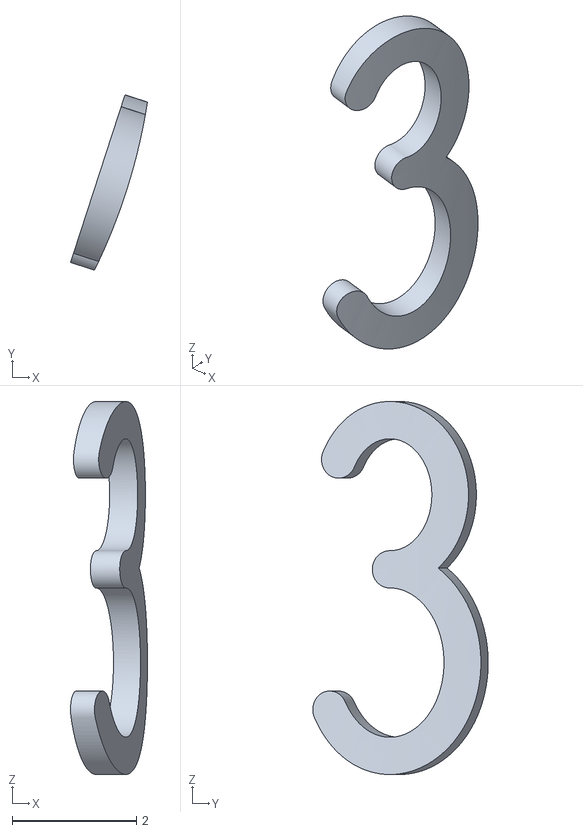
[picture p83: CAD file, 2025-07-06]
Mods/Printed Lettering/dials/results dial - digit 3.stl
1.24 x 2.82 x 6.00
