marcuswu/Curta-Type-I-3x/Mods/Printed Lettering/lower housing/Lower Housing - input 1.stl

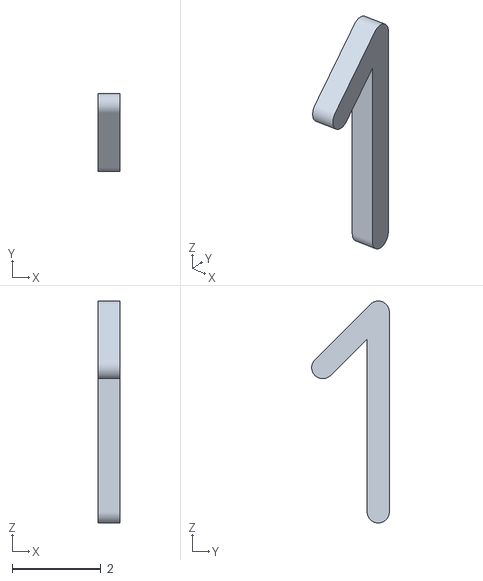
[picture p84: CAD file, 2025-07-06]
Mods/Printed Lettering/lower housing/Lower Housing - input 1.stl
0.5 x 1.75 x 5.00
