marcuswu/Curta-Type-I-3x/Mods/Printed Lettering/selector shaft top/selector shaft top - digit 6.stl

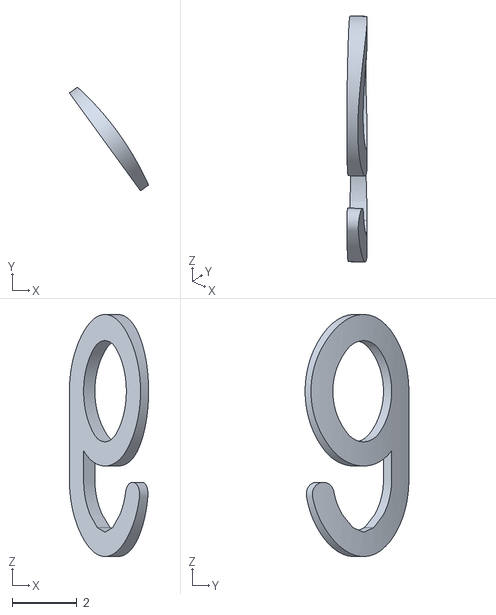
[picture p85: CAD file, 2025-07-06]
Mods/Printed Lettering/selector shaft top/selector shaft top - digit 6.stl
2.45 x 3.22 x 7.50
