marcuswu/Curta-Type-I-3x/Mods/Printed Lettering/upper housing/upper housing - digit 5.stl

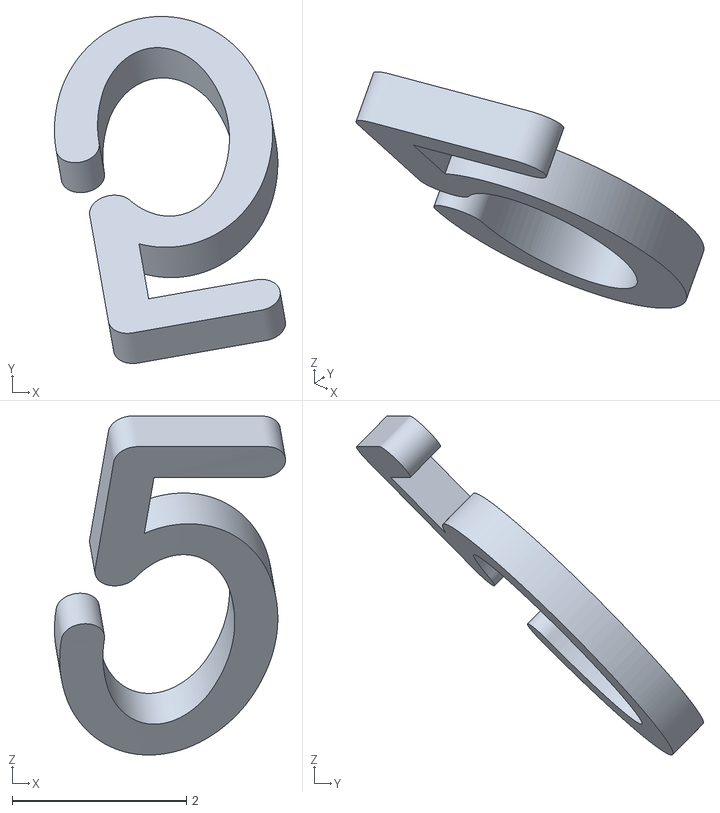
[picture p86: CAD file, 2025-07-06]
Mods/Printed Lettering/upper housing/upper housing - digit 5.stl
2.65 x 3.98 x 3.89
