marcuswu/Curta-Type-I-3x/Mods/Printed Lettering/upper outer sleeve/upper outer sleeve - C.stl

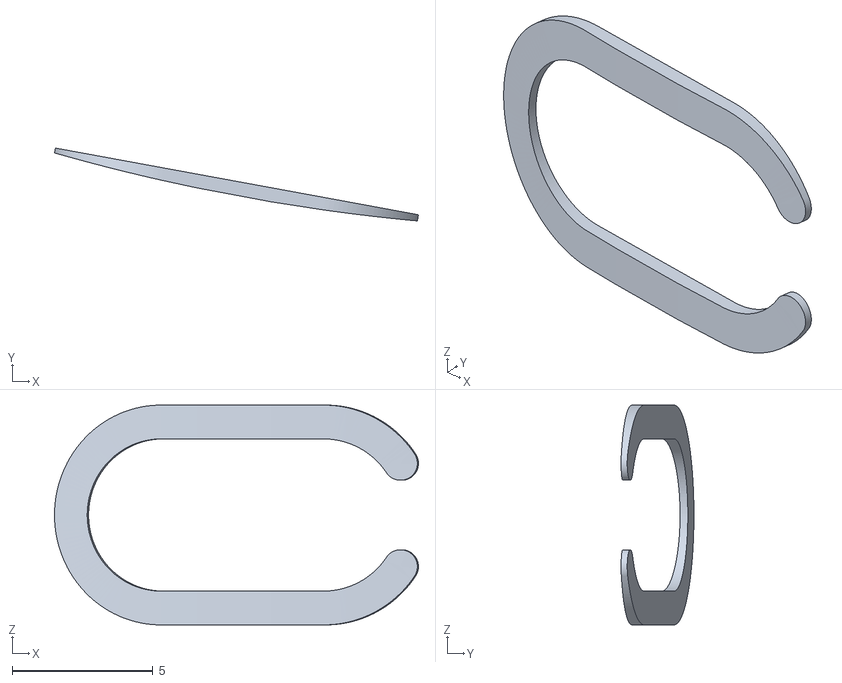
[picture p87: CAD file, 2025-07-06]
Mods/Printed Lettering/upper outer sleeve/upper outer sleeve - C.stl
12.9 x 2.59 x 7.80
