marcuswu/Curta-Type-I-3x/STLs/13 - Assemble Zero Positioning Lever/zero positioning lever.stl

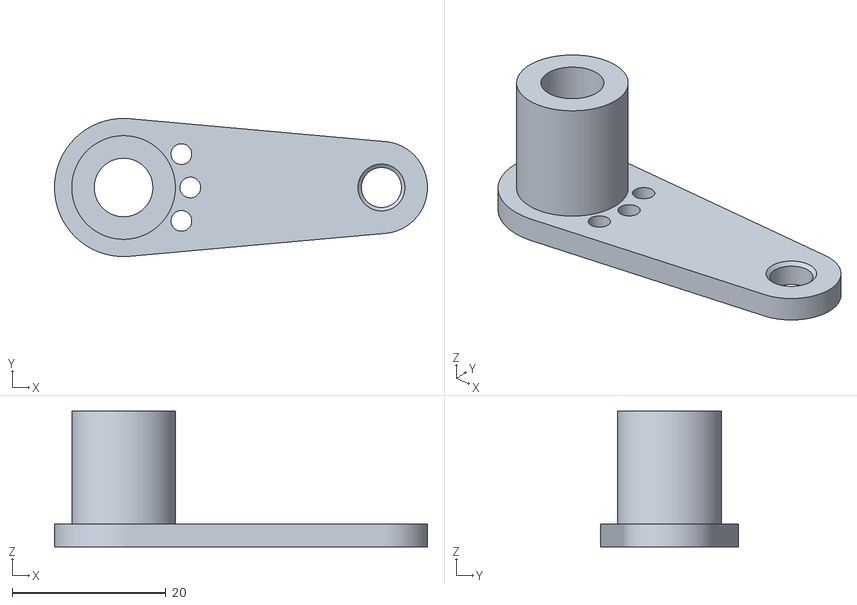
[picture p88: CAD file, 2022-03-31]
STLs/13 - Assemble Zero Positioning Lever/zero positioning lever.stl
48.6 x 18.0 x 17.7
