marcuswu/Curta-Type-I-3x/STLs/27 - Assemble Reversing Lever/reversing shaft.stl

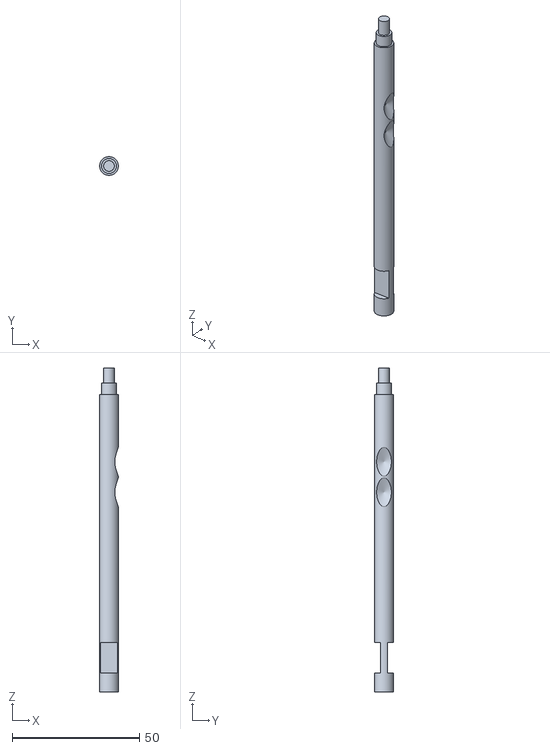
[picture p89: CAD file, 2022-03-31]
STLs/27 - Assemble Reversing Lever/reversing shaft.stl
7.39 x 7.39 x 127.5
