marcuswu/Curta-Type-I-3x/STLs/31 - Assemble Input Selectors/selector shaft bottom x8.stl

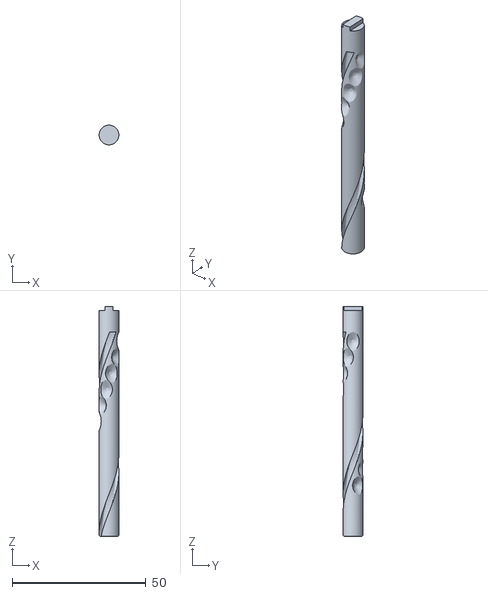
[picture p90: CAD file, 2022-03-31]
STLs/31 - Assemble Input Selectors/selector shaft bottom x8.stl
7.39 x 7.39 x 86.1
