marcuswu/Curta-Type-I-3x/STLs/37 - Clearing Cover/clearing ring rivet x2.stl

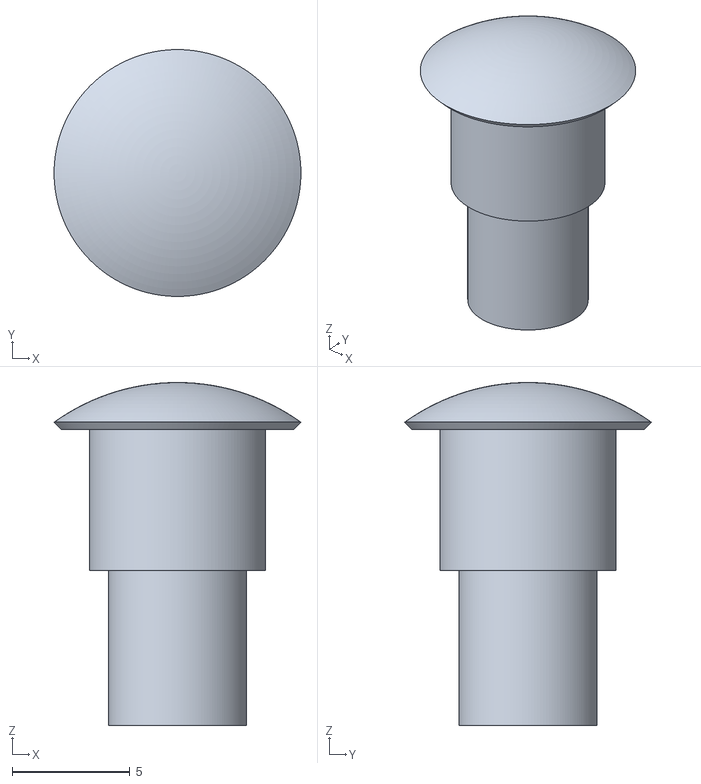
[picture p91: CAD file, 2022-03-31]
STLs/37 - Clearing Cover/clearing ring rivet x2.stl
10.5 x 10.5 x 14.6
