marcuswu/Curta-Type-I-3x/STLs/38 - Carriage Body/carriage body pin x2.stl

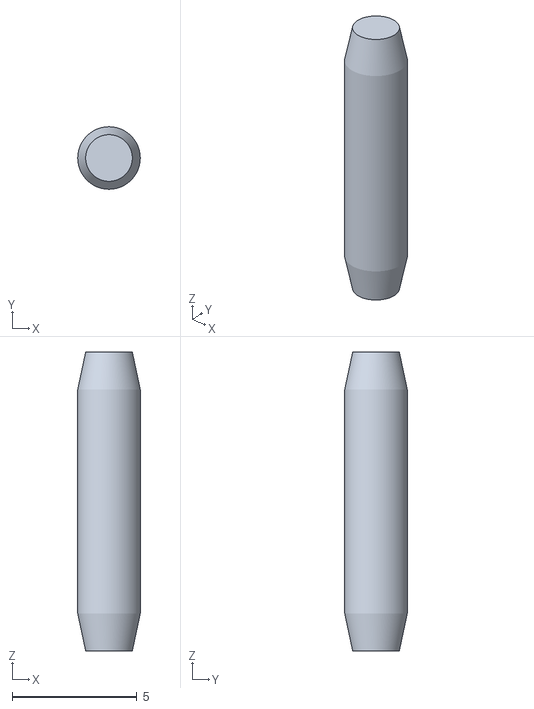
[picture p92: CAD file, 2022-03-31]
STLs/38 - Carriage Body/carriage body pin x2.stl
2.51 x 2.51 x 12.0
