marcuswu/Curta-Type-I-3x/Mods/Metal Main Shaft/rotation_blocker.stl

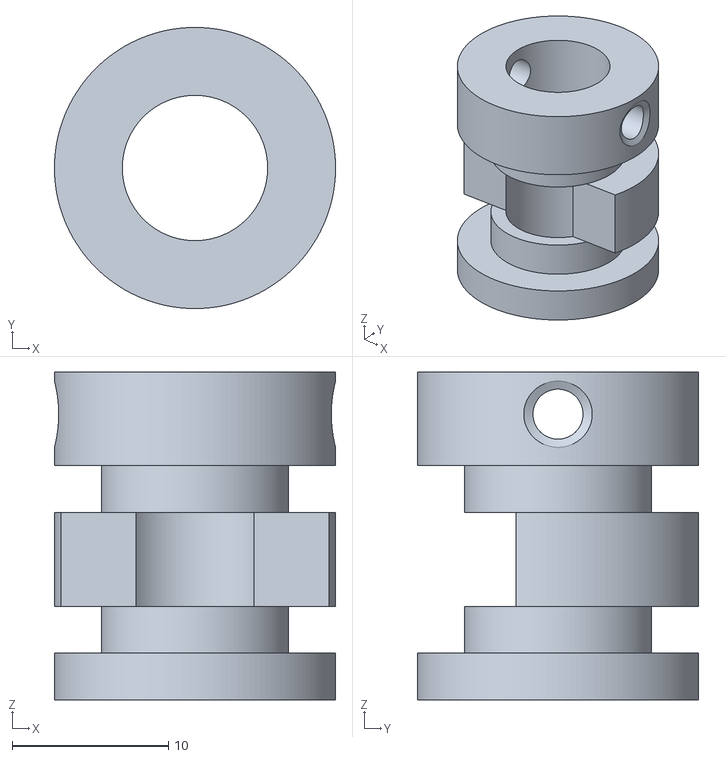
[picture p94: CAD file, 2025-07-06]
Mods/Metal Main Shaft/rotation_blocker.stl
18.0 x 18.0 x 21.0
