marcuswu/Curta-Type-I-3x/Mods/Printed Lettering/lower housing/Lower Housing - input 4.stl

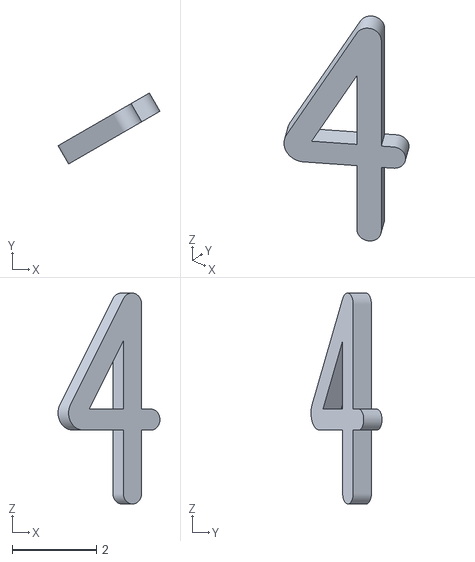
[picture p96: CAD file, 2025-07-06]
Mods/Printed Lettering/lower housing/Lower Housing - input 4.stl
2.42 x 1.68 x 5.00
