marcuswu/Curta-Type-I-3x/Mods/Printed Lettering/selector shaft top/selector shaft top - digit 1.stl

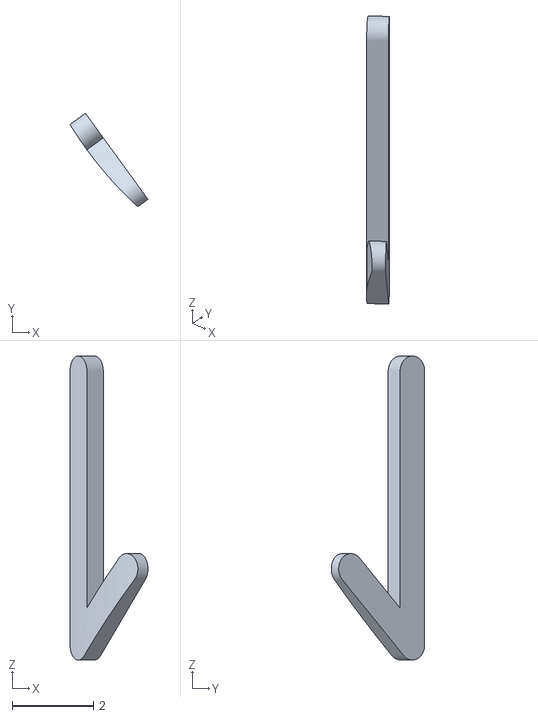
[picture p97: CAD file, 2025-07-06]
Mods/Printed Lettering/selector shaft top/selector shaft top - digit 1.stl
1.92 x 2.31 x 7.50
