marcuswu/Curta-Type-I-3x/Mods/Printed Lettering/upper housing/upper housing - digit 4.stl

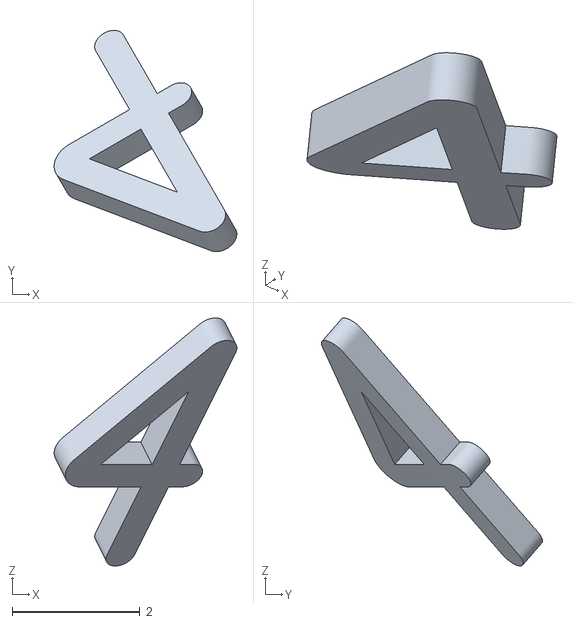
[picture p98: CAD file, 2025-07-06]
Mods/Printed Lettering/upper housing/upper housing - digit 4.stl
2.86 x 3.47 x 3.89
