marcuswu/Curta-Type-I-3x/Mods/Printed Lettering/upper outer sleeve/upper outer sleeve - Turns Arrow.stl

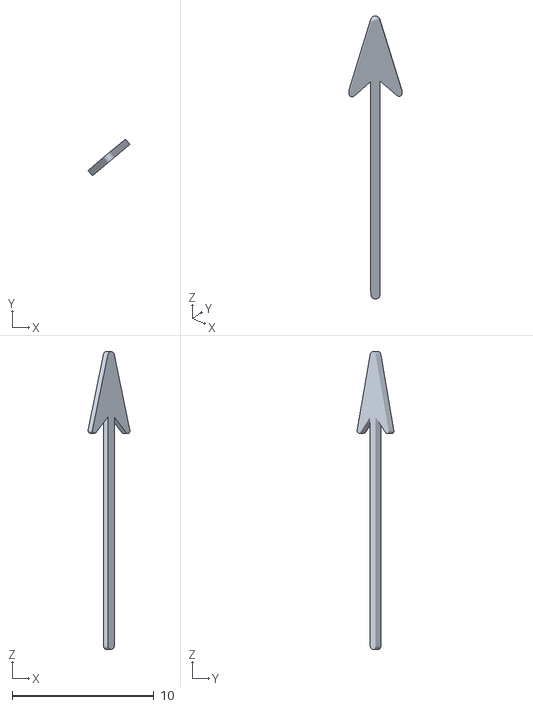
[picture p99: CAD file, 2025-07-06]
Mods/Printed Lettering/upper outer sleeve/upper outer sleeve - Turns Arrow.stl
2.95 x 2.59 x 21.0
