marcuswu/Curta-Type-I-3x/STLs/37 - Clearing Cover/clearing ring.stl

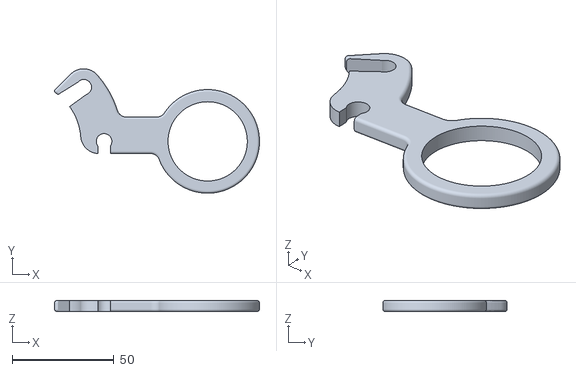
[picture p100: CAD file, 2022-03-31]
STLs/37 - Clearing Cover/clearing ring.stl
100.9 x 61.2 x 5.46
