marcuswu/Curta-Type-I-3x/Manual/Painting/Input Digits-exploded.dxf

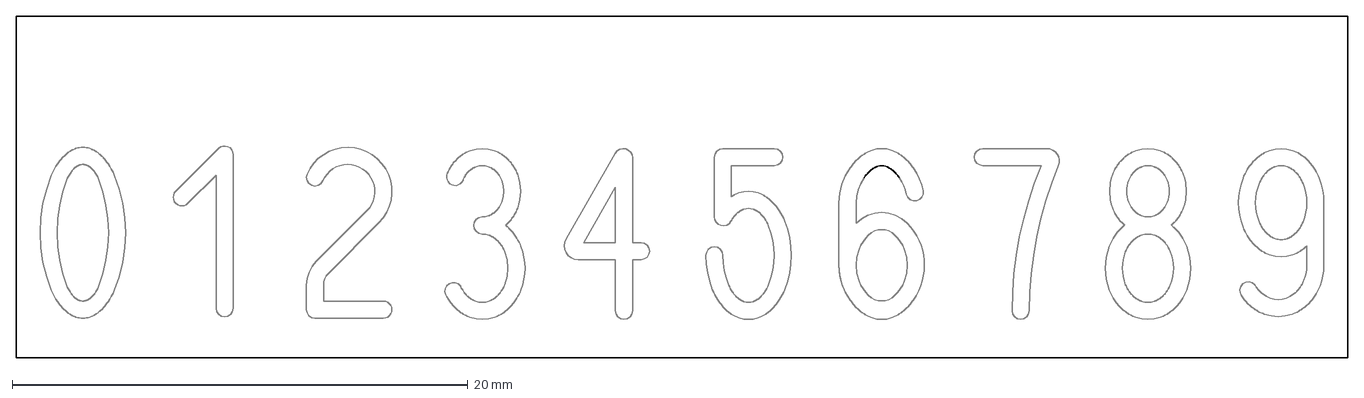
[picture p101: CAD file, 2025-07-06]
Manual/Painting/Input Digits-exploded.dxf
58.4 x 15.0 mm
