marcuswu/Curta-Type-I-3x/Mods/Printed Lettering/lower housing/Lower Housing - reversing up arrow.stl

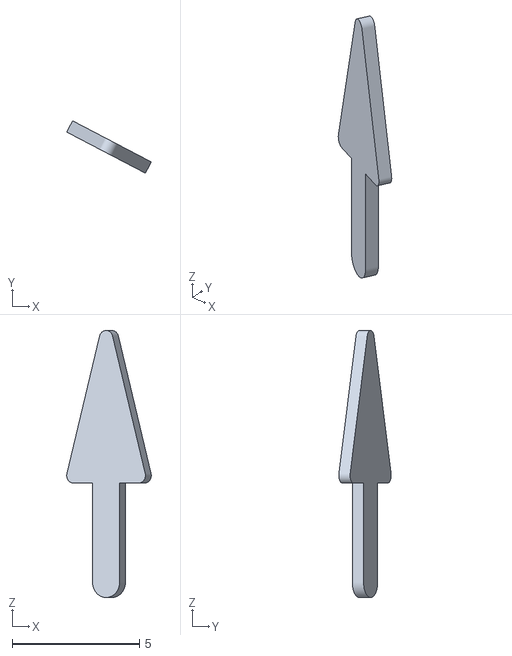
[picture p103: CAD file, 2025-07-06]
Mods/Printed Lettering/lower housing/Lower Housing - reversing up arrow.stl
3.33 x 2.06 x 10.5
