marcuswu/Curta-Type-I-3x/Mods/Printed Lettering/upper housing/upper housing - digit 10-2.stl

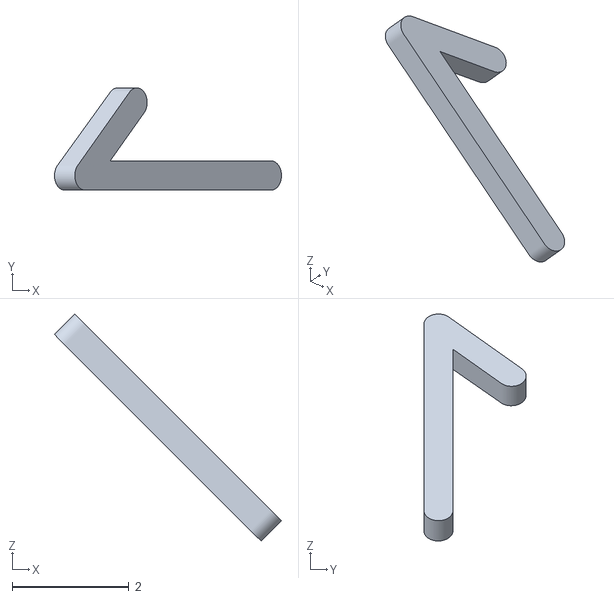
[picture p105: CAD file, 2025-07-06]
Mods/Printed Lettering/upper housing/upper housing - digit 10-2.stl
3.88 x 1.75 x 3.88
