marcuswu/Curta-Type-I-3x/Mods/Printed Lettering/upper outer sleeve/upper outer sleeve - T.stl

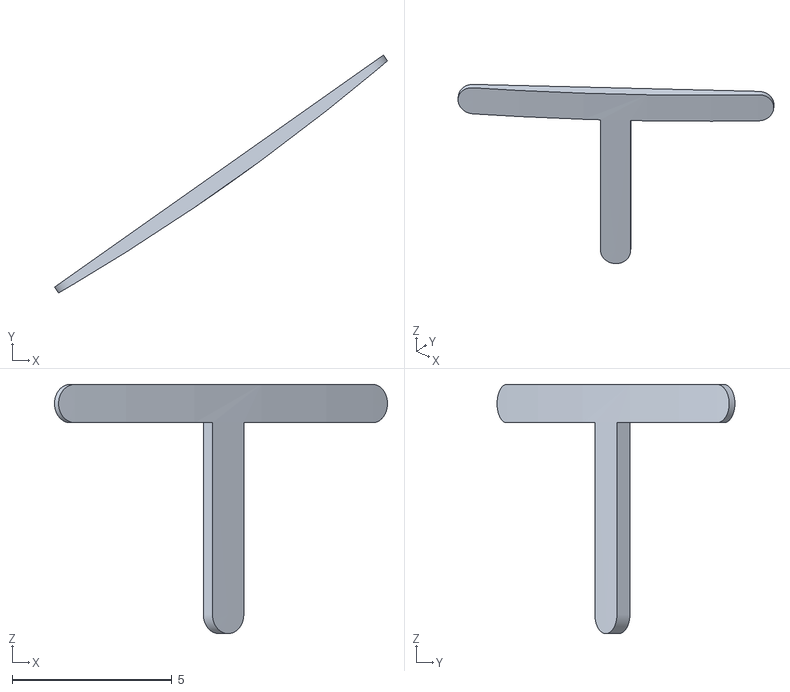
[picture p106: CAD file, 2025-07-06]
Mods/Printed Lettering/upper outer sleeve/upper outer sleeve - T.stl
10.4 x 7.45 x 7.80
