marcuswu/Curta-Type-I-3x/Manual/Painting/upper outer sleeve-cricut.dxf

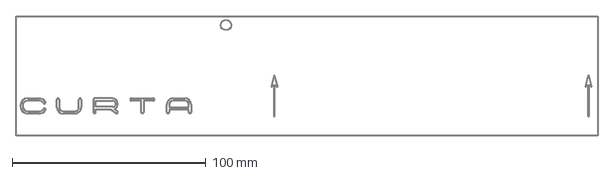
[picture p107: CAD file, 2025-07-06]
Manual/Painting/upper outer sleeve-cricut.dxf
299.7 x 61.5 mm
