marcuswu/Curta-Type-I-3x/Mods/Printed Lettering/dials/results dial - results dial type 1.stl

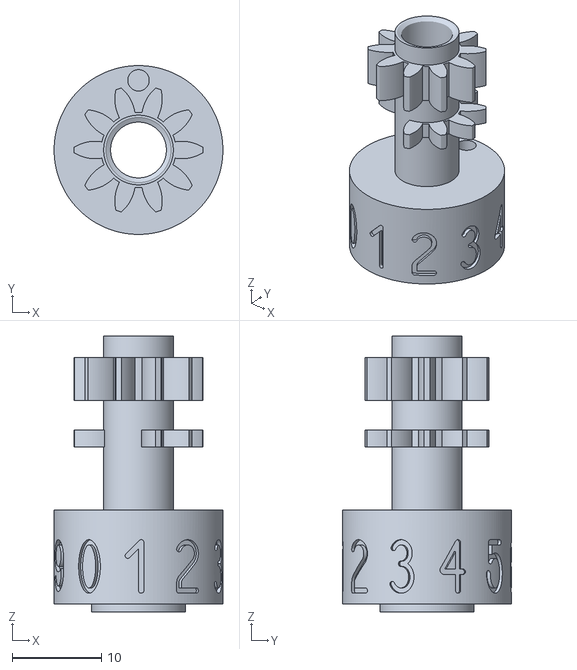
[picture p108: CAD file, 2025-07-06]
Mods/Printed Lettering/dials/results dial - results dial type 1.stl
18.9 x 18.9 x 30.9
