marcuswu/Curta-Type-I-3x/Mods/Printed Lettering/lower housing/Lower Housing - input 6.stl

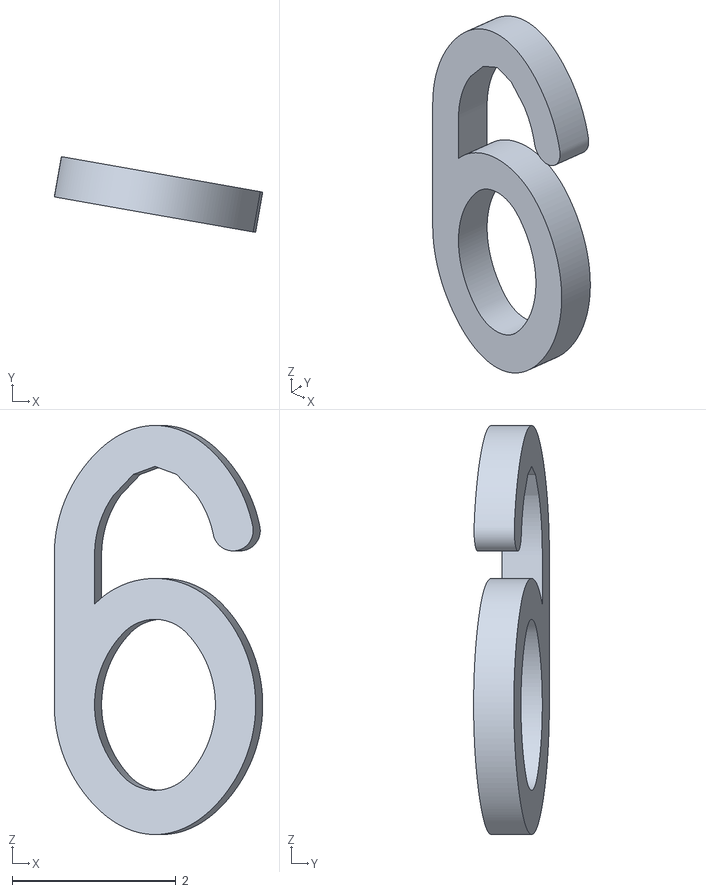
[picture p109: CAD file, 2025-07-06]
Mods/Printed Lettering/lower housing/Lower Housing - input 6.stl
2.55 x 0.926 x 5.00
