marcuswu/Curta-Type-I-3x/Mods/Printed Lettering/selector shaft top/selector shaft top - digit 2.stl

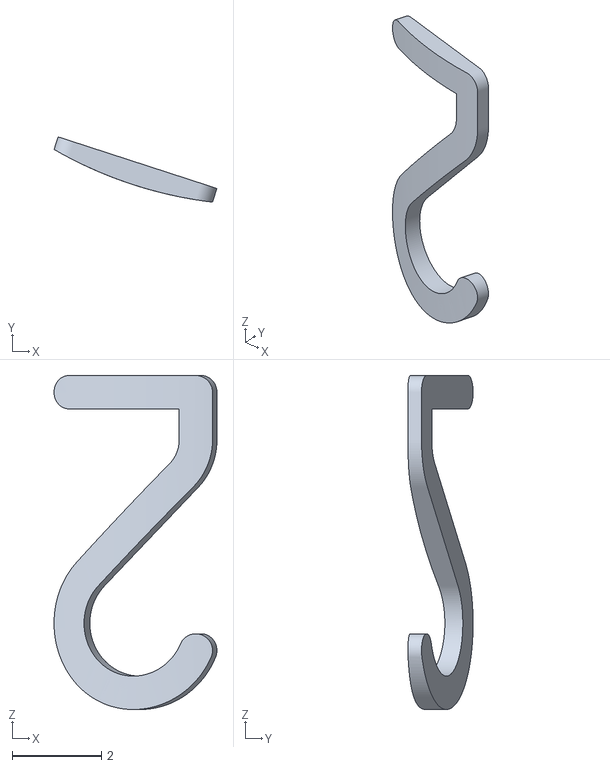
[picture p110: CAD file, 2025-07-06]
Mods/Printed Lettering/selector shaft top/selector shaft top - digit 2.stl
3.66 x 1.46 x 7.50
