marcuswu/Curta-Type-I-3x/Mods/Printed Lettering/upper housing/upper housing - digit 9.stl

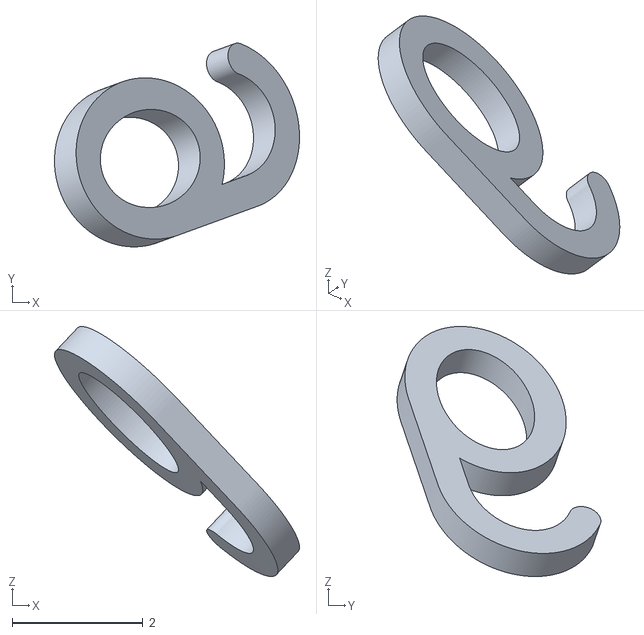
[picture p111: CAD file, 2025-07-06]
Mods/Printed Lettering/upper housing/upper housing - digit 9.stl
3.75 x 3.12 x 3.83
