marcuswu/Curta-Type-I-3x/Mods/Printed Lettering/upper outer sleeve/upper outer sleeve - Result Arrow.stl

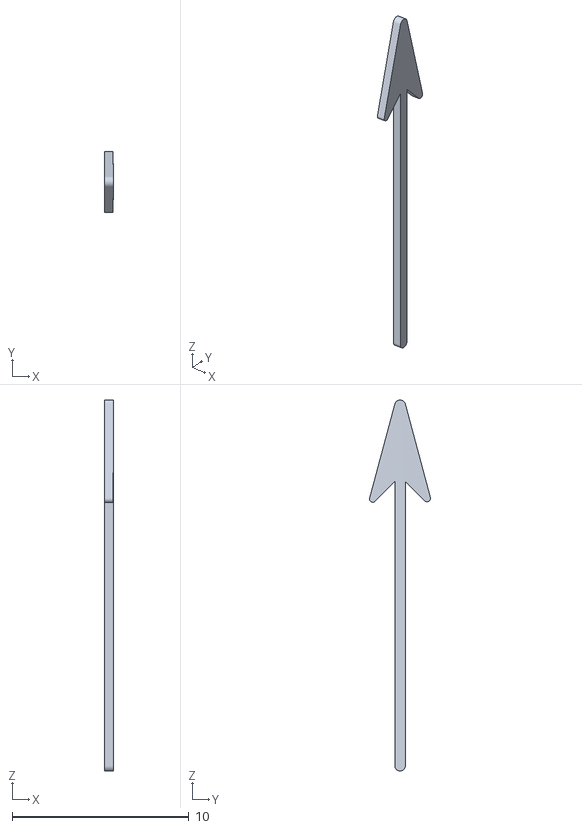
[picture p112: CAD file, 2025-07-06]
Mods/Printed Lettering/upper outer sleeve/upper outer sleeve - Result Arrow.stl
0.5 x 3.45 x 21.0
