marcuswu/Curta-Type-I-3x/Mods/Printed Lettering/dials/results dial - digit 1.stl

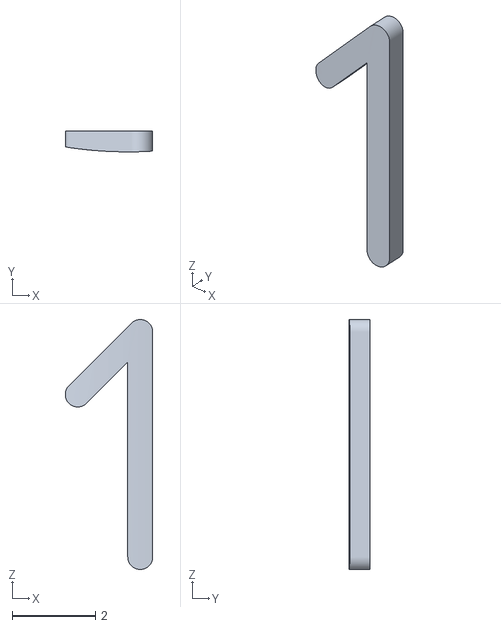
[picture p114: CAD file, 2025-07-06]
Mods/Printed Lettering/dials/results dial - digit 1.stl
2.10 x 0.5 x 6.00
