marcuswu/Curta-Type-I-3x/Mods/Printed Lettering/lower housing/Lower Housing - input 7.stl

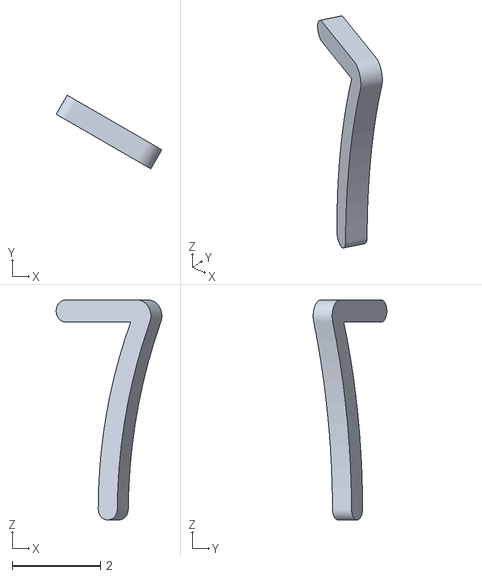
[picture p115: CAD file, 2025-07-06]
Mods/Printed Lettering/lower housing/Lower Housing - input 7.stl
2.40 x 1.68 x 5.00
