marcuswu/Curta-Type-I-3x/Mods/Printed Lettering/selector shaft top/selector shaft top - digit 4.stl

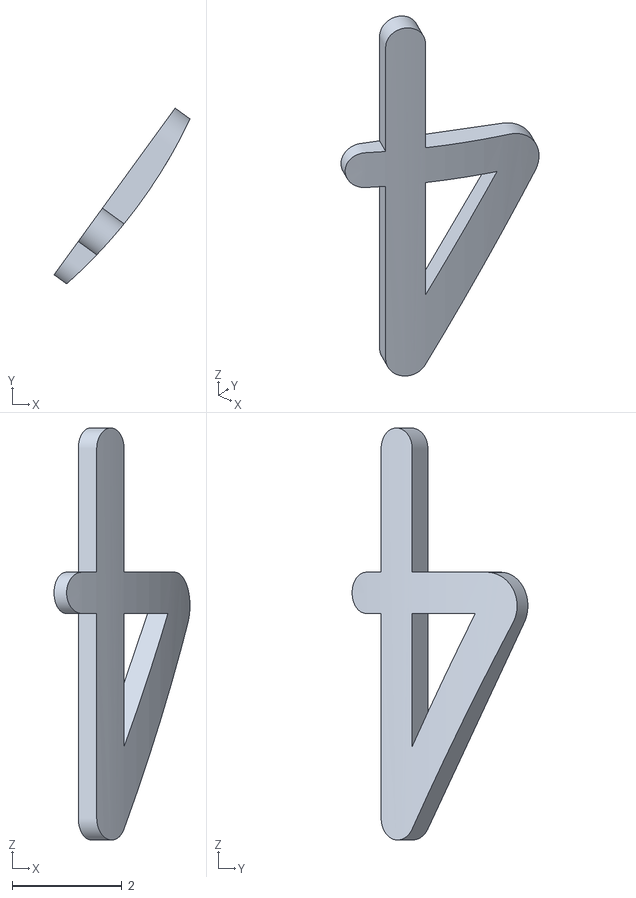
[picture p116: CAD file, 2025-07-06]
Mods/Printed Lettering/selector shaft top/selector shaft top - digit 4.stl
2.47 x 3.20 x 7.50
