marcuswu/Curta-Type-I-3x/Mods/Printed Lettering/upper housing/upper housing - digit 10-1.stl

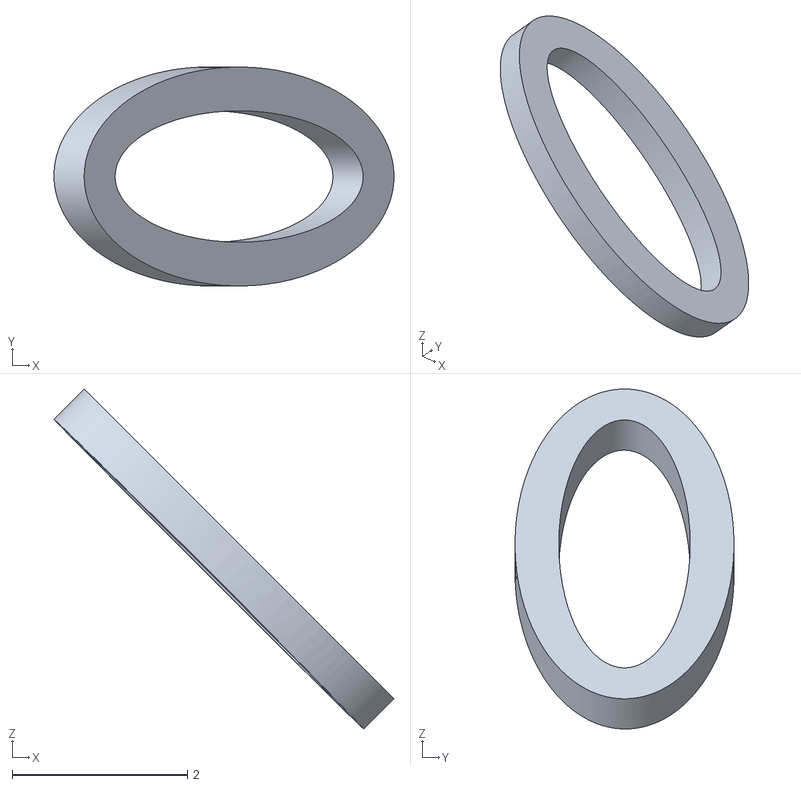
[picture p117: CAD file, 2025-07-06]
Mods/Printed Lettering/upper housing/upper housing - digit 10-1.stl
3.88 x 2.50 x 3.88
