marcuswu/Curta-Type-I-3x/Manual/Painting/reversing lever arrows-R15.dxf

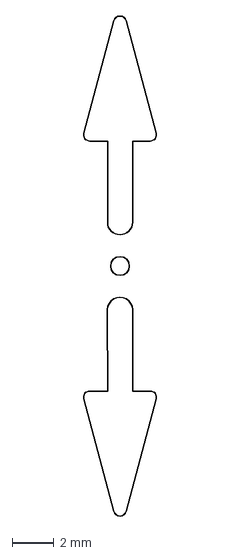
[picture p119: CAD file, 2025-07-06]
Manual/Painting/reversing lever arrows-R15.dxf
3.52 x 24.0 mm
