marcuswu/Curta-Type-I-3x/Mods/Printed Lettering/dials/results dial - digit 5.stl

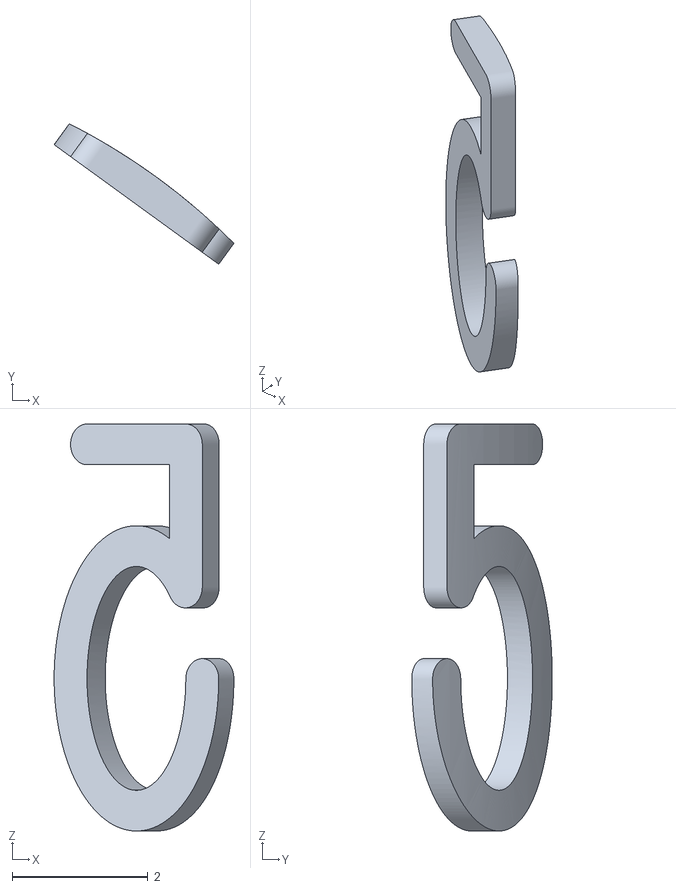
[picture p120: CAD file, 2025-07-06]
Mods/Printed Lettering/dials/results dial - digit 5.stl
2.65 x 2.07 x 6.00
