marcuswu/Curta-Type-I-3x/Mods/Printed Lettering/lower housing/Lower Housing - input 8.stl

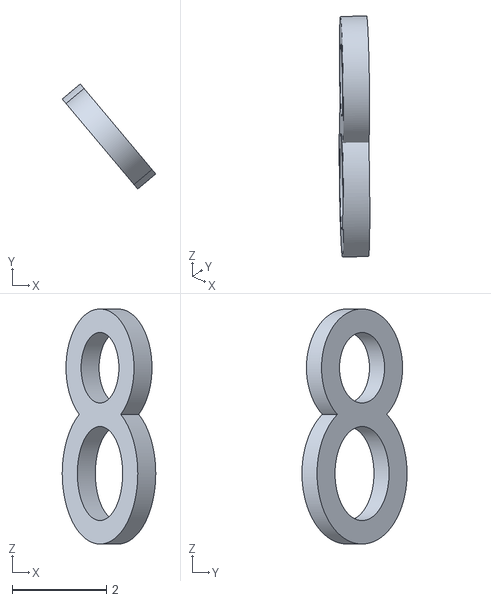
[picture p121: CAD file, 2025-07-06]
Mods/Printed Lettering/lower housing/Lower Housing - input 8.stl
1.99 x 2.24 x 5.00
