marcuswu/Curta-Type-I-3x/Mods/Printed Lettering/selector shaft top/selector shaft top - digit 8.stl

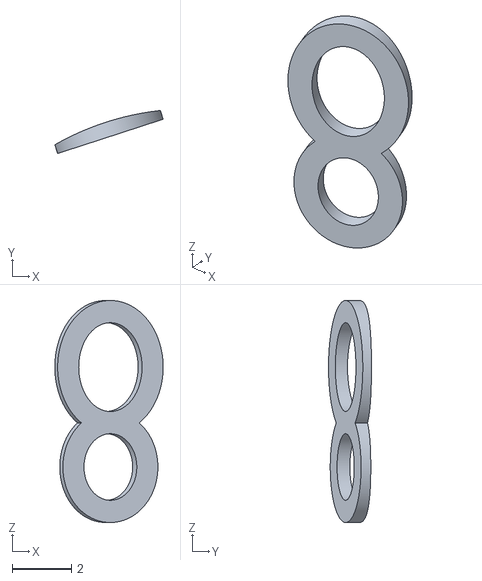
[picture p122: CAD file, 2025-07-06]
Mods/Printed Lettering/selector shaft top/selector shaft top - digit 8.stl
3.66 x 1.45 x 7.50
