marcuswu/Curta-Type-I-3x/Manual/Painting/5mm digits.dxf

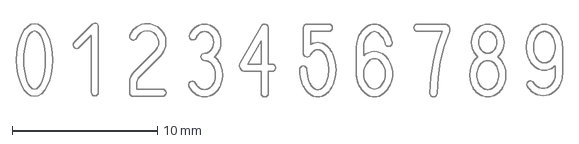
[picture p124: CAD file, 2025-07-06]
Manual/Painting/5mm digits.dxf
37.6 x 5.12 mm
