marcuswu/Curta-Type-I-3x/Mods/Printed Lettering/dials/mmu results dial type 1.3mf

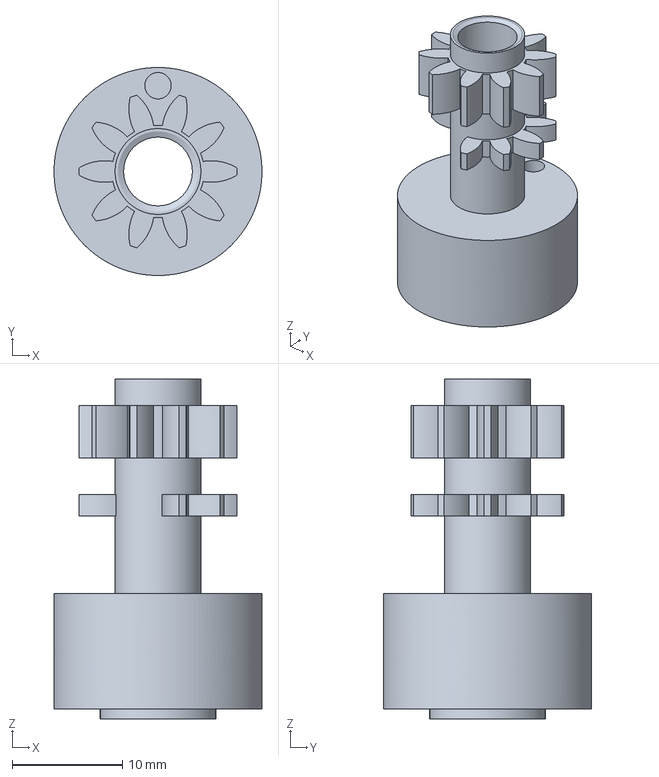
[picture p125: CAD file, 2025-07-06]
Mods/Printed Lettering/dials/mmu results dial type 1.3mf
18.9 x 18.9 x 30.9 mm
