marcuswu/Curta-Type-I-3x/Mods/Printed Lettering/lower housing/Lower Housing - reversing center dot.stl

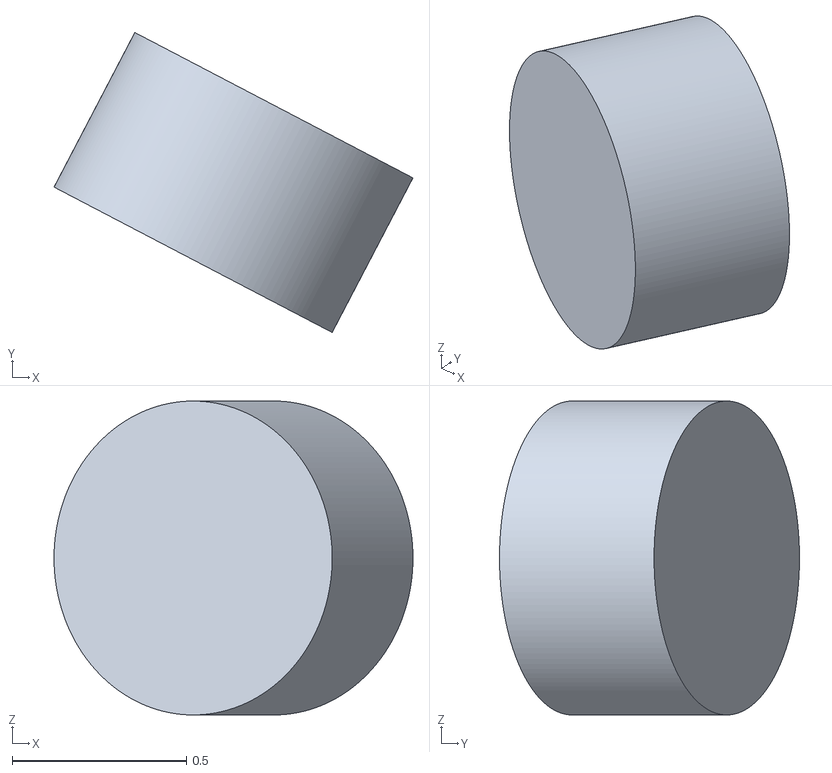
[picture p126: CAD file, 2025-07-06]
Mods/Printed Lettering/lower housing/Lower Housing - reversing center dot.stl
1.03 x 0.86 x 0.9
