marcuswu/Curta-Type-I-3x/Mods/Printed Lettering/selector shaft top/selector shaft top - digit 7.stl

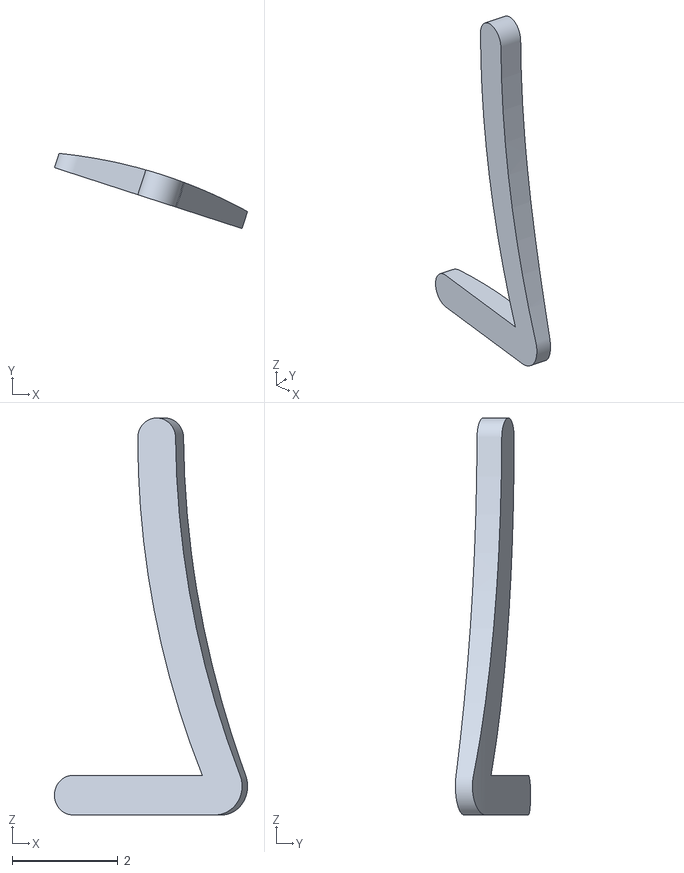
[picture p127: CAD file, 2025-07-06]
Mods/Printed Lettering/selector shaft top/selector shaft top - digit 7.stl
3.65 x 1.42 x 7.50
