marcuswu/Curta-Type-I-3x/Mods/Printed Lettering/upper housing/upper housing - digit 11-1.stl

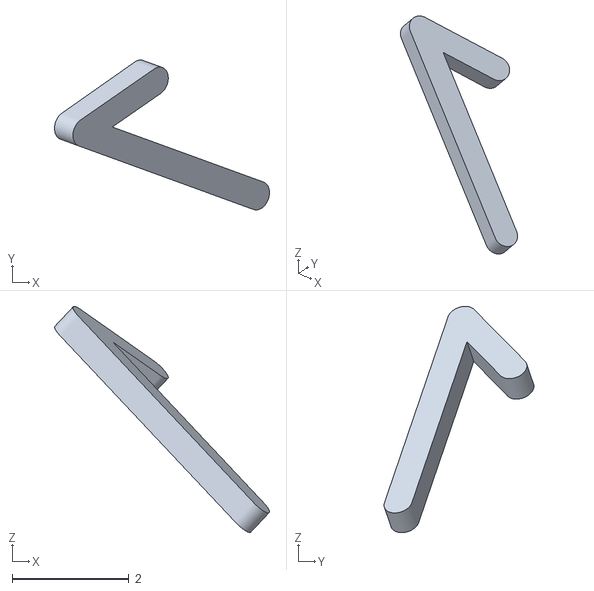
[picture p128: CAD file, 2025-07-06]
Mods/Printed Lettering/upper housing/upper housing - digit 11-1.stl
3.68 x 2.57 x 3.87
