marcuswu/Curta-Type-I-3x/Mods/Printed Lettering/dials/results dial - digit 9.stl

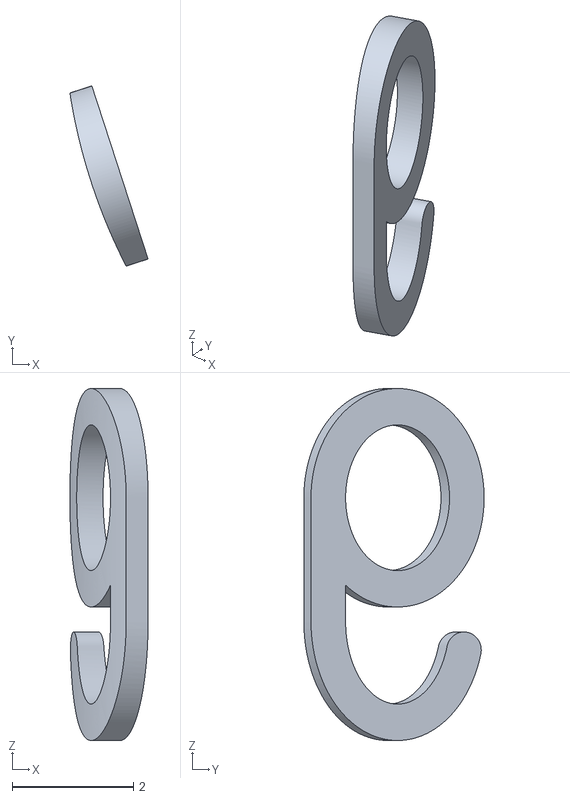
[picture p129: CAD file, 2025-07-06]
Mods/Printed Lettering/dials/results dial - digit 9.stl
1.29 x 2.97 x 5.80
