marcuswu/Curta-Type-I-3x/Mods/Printed Lettering/selector shaft top/selector shaft top - digit 3.stl

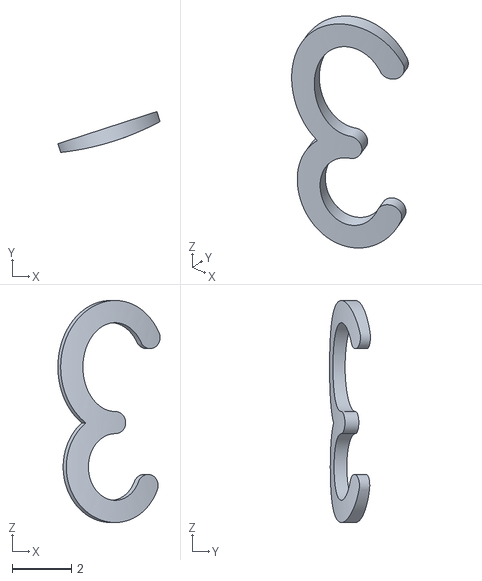
[picture p130: CAD file, 2025-07-06]
Mods/Printed Lettering/selector shaft top/selector shaft top - digit 3.stl
3.45 x 1.38 x 7.50
