marcuswu/Curta-Type-I-3x/Mods/Printed Lettering/upper housing/upper housing - digit 2.stl

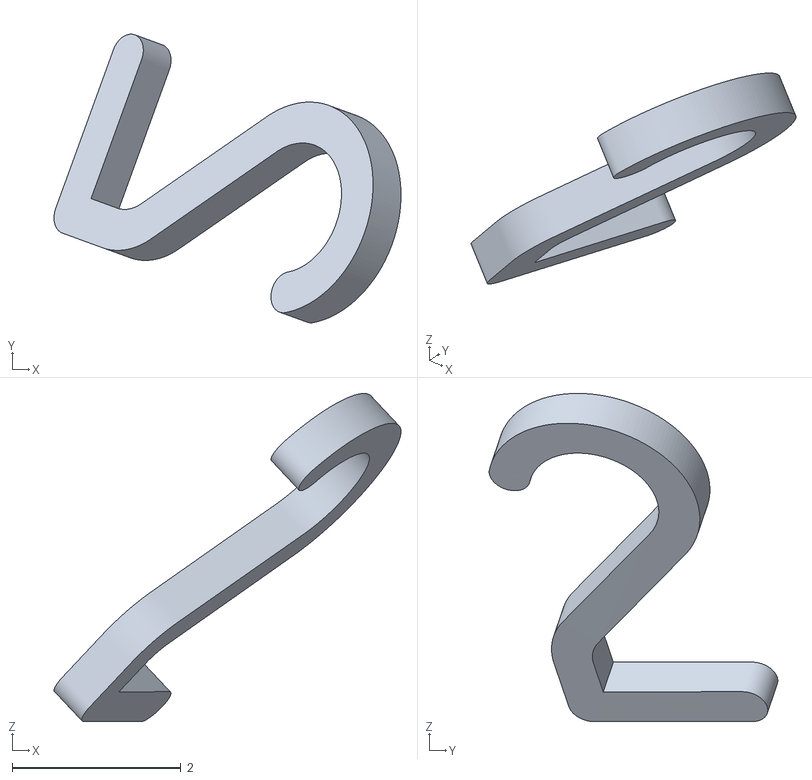
[picture p131: CAD file, 2025-07-06]
Mods/Printed Lettering/upper housing/upper housing - digit 2.stl
4.11 x 3.42 x 3.89
