marcuswu/Curta-Type-I-3x/Mods/Printed Lettering/dials/results dial - digit 6.stl

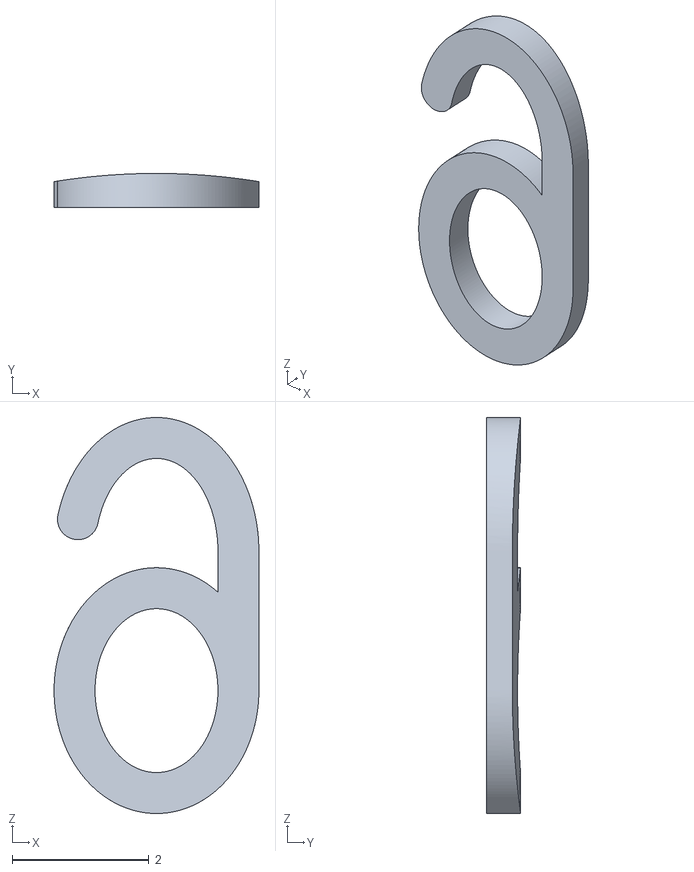
[picture p134: CAD file, 2025-07-06]
Mods/Printed Lettering/dials/results dial - digit 6.stl
3.00 x 0.5 x 5.80
