marcuswu/Curta-Type-I-3x/Mods/Printed Lettering/upper housing/mmu upper housing.3mf

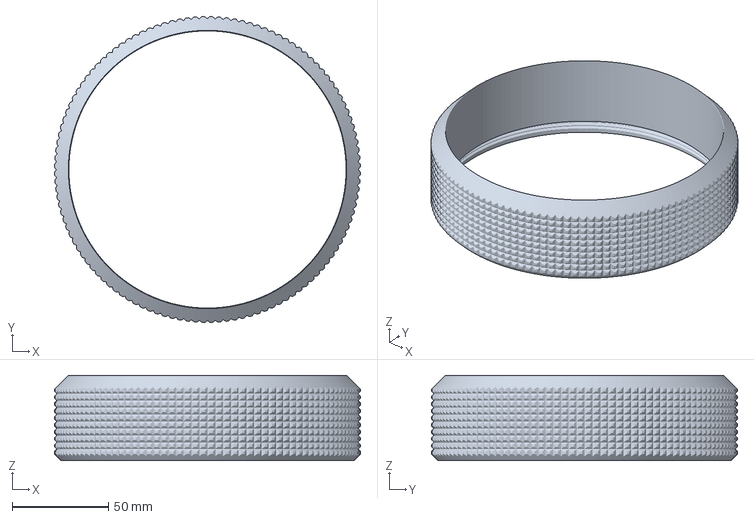
[picture p135: CAD file, 2025-07-06]
Mods/Printed Lettering/upper housing/mmu upper housing.3mf
159.0 x 159.0 x 44.4 mm
